pchambre/PC1500ExpansionModule/RP2350/monitor.c

/* monitor.c
 *
 * Ported from Design01_NonDMA_8K_PV_Swap.cydsn/main.c -- see that file
 * and this repo's plan history for the full background. Two halves,
 * now running on separate cores (changed 2026-09-17 -- see below):
 *
 *   1. monitor_run()'s bus loop (core0): on the GreenPAK's read-trigger
 *      (CS && Read && OE), drive the data pins from buffer[page][laddress];
 *      on the write-trigger (CS && Write), latch data into the buffer, or
 *      hand off to core1 if the write landed on the instruction address.
 *      Direct SIO register reads throughout (sio_hw->gpio_in/gpio_out/
 *      gpio_oe), not per-pin gpio_get()/gpio_put() calls -- those go
 *      through more machinery than a ~2us budget can afford. This loop
 *      never blocks, not even for a command's duration.
 *   2. monitor_command_worker()'s DoCommand() (core1): the same ~30-case
 *      EXP_COMMAND_* switch, translated case-by-case from SEGGER emFile's
 *      FS_* API to FatFs's f_* API. Blocks core1 for a command's whole
 *      duration; core0 is unaffected and keeps servicing the bus.
 *
 * RAM RESIDENCY -- deliberately NOT applied here. DoCommand() and this
 * file's loop don't need __not_in_flash_func the way qmi_cs1_spi.c/
 * qmi_cs1_sd.c do -- those needed it to keep their own internal per-byte
 * transfer loops from deadlocking against their own open QMI transaction
 * (see their own top comments), a QMI-specific hazard this design never
 * had to think about at all.
 *
 * WHY TWO CORES (changed 2026-09-17, was single-core): the original
 * single-core design had core0 call DoCommand() directly from inside the
 * bus loop, blocking the whole loop for the command's duration -- on the
 * theory (matching the PSoC5 original, which really does work this way)
 * that any bus read landing on the status byte *while DoCommand() runs*
 * would see whatever was last physically latched on the data pins, and
 * the ROM-side poll loop would just keep spinning until a real answer
 * came back once DoCommand() returned. That theory doesn't hold on this
 * board: this design releases the data bus to Hi-Z with a pull-DOWN
 * between transactions (see InitGpio()'s own comment), so "whatever was
 * last latched" during a long DoCommand() call is actually a floating
 * bus reading as 0x00 -- which is EXP_STATUS_READY's own value (see
 * pc_exp.h), completely indistinguishable from a real "done" answer.
 * Confirmed live 2026-09-17: SDLS's own SD_LIST_POLL busy-wait (rom.asm)
 * would see this false READY almost immediately, read directory data
 * DoCommand() hadn't written yet, and crash with a different garbage-
 * triggered BASIC error (ERROR 40/120/122, never the same one twice)
 * every time. A same-core fix (core0 explicitly driving EXP_STATUS_BUSY
 * and holding it for the whole call) was tried first and worked, but
 * still left core0 unable to service anything else for a command's whole
 * duration -- moving DoCommand() to core1 removes that limitation
 * entirely rather than just papering over its one known symptom.
 */
#include "monitor.h"

#include <stdio.h>
#include <string.h>

#include "hardware/structs/sio.h"
#include "hardware/gpio.h"
#include "hardware/sync.h"
#include "hardware/pio.h"
#include "hardware/dma.h"
#include "pico/stdlib.h"
#include "pico/time.h"
#ifndef PC1500_NO_CYW43
#include "pico/cyw43_arch.h"
/* The activity LED: a CYW43 GPIO on the dongle. */
#define LED_PUT(on) cyw43_arch_gpio_put(CYW43_WL_GPIO_LED_PIN, (on))
#else
#define LED_PUT(on) ((void)(on)) /* the internal card has no LED (2026-10-09) */
#endif
#include "pico/multicore.h"
#include "pico/low_power.h"
#include "pico/aon_timer.h"
#include "hardware/powman.h"
#include "hardware/watchdog.h"
#include "hardware/structs/scb.h"

#include "ff.h"
#include "board_pins.h"
#include "pc_exp.h"
#include "greenpak_i2c.h"
#include "greenpak_virtual_io.h"
#include "mcu_log.h"
#include "keywords.h"
#include "kbd_seq.h"
#include "kbd_host.h"
#include "ble_link.h"
#include "wifi_link.h"
#include "ssh_session.h"
#include "net_ping.h"
#include "time_sync.h"
#include "history_session.h"
#include "basic_xlate.h"
#include "mcu_config.h"
#include "mcu_store.h"
#include "read_serve.pio.h"
#include "write_serve.pio.h"

/* rom_image.h is generated by ../Design01_NonDMA_8K_PV_Swap.cydsn/rom/
 * build.ps1 from rom.asm -- the LH5801-side ROM content is identical
 * regardless of which MCU serves it, so this includes that same
 * generated file directly (CMakeLists.txt adds its directory to the
 * include path) rather than hand-copying it, so it can never drift from
 * the PSoC5 side. It uses PSoC's uint8/uint16 typedefs (normally pulled
 * in via project.h there); #define'd here just for this include so the
 * generated file itself doesn't need touching. */
#define uint8 uint8_t
#define uint16 uint16_t
#include "rom_image.h"
#undef uint8
#undef uint16

/* ---- Shared 8K data window: pages 0-7 (2K live data window) plus
 * pages 8-31 (6K ROM region, only actually driven through this buffer
 * while Control_Mode_Control-equivalent GreenPAK state selects
 * ROM_FROM_MCU during the boot copy -- see PC_EXP.h's own top comment).
 *
 * 8192-byte aligned (2026-09-18) -- the PIO-driven read path
 * (read_serve.pio's addr_capture program, see SetupReadServePio() below)
 * builds a complete absolute RAM address by shifting a fixed prefix (this
 * buffer's own high address bits) ahead of the live 13-bit address bus
 * value. That only produces the right address if this buffer's base
 * address has all ADDR_PIN_COUNT low bits clear -- i.e. is aligned to its
 * own size (8192 = 2^13). GCC/Clang's `aligned` attribute on a static
 * array guarantees the linker places it on that boundary. */
static uint8_t buffer[32][256] __attribute__((aligned(8192)));

/* Command watchdog, checked by core0 (never core1 -- core1 may be deep
 * inside a blocked call and can't watch its own clock). `buffer`'s status
 * byte is the single source of truth for "a command is in flight" (==
 * EXP_STATUS_BUSY); g_command_start_us is only meaningful while that's
 * true, refreshed every time core0 dispatches a new command. This is a
 * backstop, not the primary fix -- greenpak_i2c.c's own I2C_SCL_TIMEOUT_US
 * bound (2026-09-17) already converts the one known unbounded hang into a
 * fast, clean failure. This catches anything that's merely slow (or any
 * future bug in the same class) by forcing the status to ERROR once a
 * command has been running too long, so the LH5801's own busy-poll loop
 * (which has no timeout of its own) always gets an answer.
 *
 * Widened from the original 2s (2026-09-17) -- that value was chosen for
 * SDLS specifically and directly broke the DOSTUFF isolation test it was
 * never meant to cover: DOSTUFF 5/8 were firing this watchdog at 2s,
 * forcing ERROR while core1 kept legitimately sleeping in the background,
 * then racing core1's own late real WriteStatus() against this one for
 * whichever value the LH5801's next poll happened to sample -- exactly
 * the inconsistent BAD STATUS/OK results seen live. 30s comfortably
 * covers DOSTUFF's own test range; this still needs to become per-command
 * eventually (SDLS itself only needs ~2s worst case -- see
 * diskio_sd.c's SD_INIT_TIMEOUT_US -- so 30s is far looser than
 * ideal for real commands, just deliberately out of DOSTUFF's way for now).
 * NOTE: this does not free up core1 if it's genuinely wedged -- it only
 * lets the bus/LH5801 side recover. A wedged core1 still won't process
 * any later command until reset, unless/until the low-level blocking
 * calls are changed to cooperatively check an abort flag themselves. */
#define COMMAND_TIMEOUT_US 30000000u
static uint32_t g_command_start_us = 0;

/* See monitor.h's own comment. Definition lives here since monitor_run()
 * (this file) is the only reader/toggler; greenpak_i2c.c is the writer. */
volatile bool g_i2c_activity_pending = false;

/* See monitor.h's own comment. Definition lives here since monitor_run()
 * is the only reader; WriteStatus() (this file, below) is the writer. */
volatile bool g_command_done_pending = false;

/* Ported from Design01_NonDMA_8K_PV_Swap.cydsn/main.c's InitBuffer/
 * LoadRomImage: zeroes the shared window, then memcpys each sparse
 * chunk of kRomImageData into place at its kRomImageChunks offset.
 * Must run before monitor_run() starts servicing bus reads (main.c's
 * job, before launching core1) -- otherwise the ROM region reads back
 * as whatever main.c's caller catches. */
void monitor_init_buffer(void) {
    memset(buffer, 0, sizeof(buffer));
    const uint8_t *src = kRomImageData;
    uint8_t *base = &buffer[0][0];
    for (size_t i = 0; i < sizeof(kRomImageChunks) / sizeof(kRomImageChunks[0]); i++) {
        memcpy(base + kRomImageChunks[i].offset, src, kRomImageChunks[i].length);
        src += kRomImageChunks[i].length;
    }
    /* READY is no longer 0 (pc_exp.h, 2026-09-24), so the memset above no
     * longer leaves the status cell reading READY by accident. */
    buffer[EXP_INSTRUCTION_PAGE][EXP_INSTRUCTION_ADDRESS] = EXP_STATUS_READY;
}

static FIL currentFile;
static bool currentFileOpen = false;
static uint8_t currentFileStatus = EXP_SD_FILE_STATUS_CLOSED;
static uint32_t fileEnd = 0;
static char currentFileName[64];

/* After a POWMAN wake (MCONF POWMANDELAY, "STAGE RAM sleep" below): the
 * directory to go back to at the first SD command. core1. */
static char g_cwd_restore[20 + 1];

static FIL channelFile[EXP_MAX_SD_CHANNELS];
static bool channelOpen[EXP_MAX_SD_CHANNELS];
static char channelName[EXP_MAX_SD_CHANNELS][EXP_PATH_ARG_LEN + 1];
static uint32_t channelReadPos[EXP_MAX_SD_CHANNELS];

/* See monitor.h. The FIL objects themselves need no closing: FatFs
 * re-mounts the new card with a fresh volume id, so any operation on an
 * old handle already fails with FR_INVALID_OBJECT. */
void monitor_sd_card_changed(void) {
    currentFileOpen = false;
    currentFileStatus = EXP_SD_FILE_STATUS_CLOSED;
    fileEnd = 0;
    for (int i = 0; i < EXP_MAX_SD_CHANNELS; i++) {
        channelOpen[i] = false;
        channelReadPos[i] = 0;
    }
}

/* STAGE keyword state (2026-09) -- GreenPAK1/GreenPAK2 share one
 * physical I2C bus (board_pins.h's PIN_GREENPAK1_SDA/SCL alias), so one
 * bus struct serves both chips, distinguished by addr7 per call.
 * romCopyActive/romCopyBlockIndex track an in-progress
 * ROM_COPY_BEGIN..GET_BLOCK*..FINISH sequence so GET_BLOCK can refuse a
 * call that arrives without a matching BEGIN (or after 6 blocks already
 * landed), and so FINISH/a later FROM_MCU can reset it. */
static const greenpak_i2c_bus_t g_greenpak_bus = {
    .sda_gpio = PIN_GREENPAK1_SDA,
    .scl_gpio = PIN_GREENPAK1_SCL,
};
static bool romCopyActive = false;
static uint16_t romCopyBlockIndex = 0;

/* True only after a full STAGE copy finished with a matching whole-ROM
 * checksum (ROM_COPY_FINISH success) and nothing has since reverted or
 * restarted it (2026-09-24). Remap alone can't answer "is the SRAM copy
 * good?" -- a failed STAGE DEBUG deliberately leaves Remap engaged over a
 * partial copy -- so ROM_GET_MODE reports this alongside Remap, letting
 * the ROM's boot hook (and STAGE RAM) skip re-staging on every reset/power-
 * on. Cleared at RP2350 boot too, matching monitor_init_greenpak()'s own
 * forced Remap-off. */
static volatile bool romStagedVerified = false; /* written by core1, read by core0 (sleep decisions) */

/* Set by core1's EXP_COMMAND_DONE (only while romStagedVerified), consumed
 * by core0's monitor_run() loop -- see the "STAGE RAM sleep" section. */
static volatile bool g_sleep_requested = false;
/* When DONE set g_sleep_requested -- the MCONF SLEEPWAIT delay counts from
 * here. */
static volatile uint32_t g_sleep_requested_us;

/* Boot-time problem for MLOG, if any -- monitor_init_greenpak() runs
 * before mcu_log_init() and before core1 exists, so it can't write the
 * flash-backed log itself; monitor_command_worker() logs it on start. */
static const char *g_boot_remap_log = NULL;

/* See monitor.h's own comment. Keeps a staged ROM across a power cycle
 * (2026-09-25, board owner's call): the GreenPAKs and the SRAM stay powered
 * from VGG while the PC-1500 -- and now the Pico with it -- is off, so a
 * finished STAGE survives. Trusted when both Remap bits are set and GP1's
 * write-enable is clear (FINISH clears WE, so a set WE means the copy was
 * interrupted). Anything else reverts all three virtual inputs to MCU-
 * served ROM, as this function always used to unconditionally: a failed or
 * interrupted STAGE otherwise leaves Remap on over half-written SRAM, and
 * that survives an RP2350 reset. Remap bits that disagree, or a set WE, are
 * logged. Known gap: a STAGE DEBUG whose final checksum failed leaves Remap
 * on and WE clear over a bad copy, and is trusted here. */
void monitor_init_greenpak(void) {
    greenpak_i2c_init(&g_greenpak_bus);
    romCopyActive = false;

    bool remap1 = false, remap2 = false, we = false;
    bool ok = greenpak_virtual_input_get(&g_greenpak_bus, GREENPAK_GP1_I2C_ADDR, GP1_VI_SRAM_ROM_REMAP, &remap1)
           && greenpak_virtual_input_get(&g_greenpak_bus, GREENPAK_GP2_I2C_ADDR, GP2_VI_SRAM_ROM_REMAP, &remap2)
           && greenpak_virtual_input_get(&g_greenpak_bus, GREENPAK_GP1_I2C_ADDR, GP1_VI_SRAM_ROM_WE, &we);
    if (ok && remap1 && remap2 && !we) {
        romStagedVerified = true; /* keep the staged ROM -- the boot hook skips the copy */
        return;
    }

    if (!ok) g_boot_remap_log = "BOOT GP read failed";
    else if (remap1 != remap2) g_boot_remap_log = "BOOT GP1/GP2 remap diff";
    else if (we) g_boot_remap_log = "BOOT copy incomplete";
    greenpak_virtual_input_set(&g_greenpak_bus, GREENPAK_GP1_I2C_ADDR, GP1_VI_SRAM_ROM_REMAP, false);
    greenpak_virtual_input_set(&g_greenpak_bus, GREENPAK_GP2_I2C_ADDR, GP2_VI_SRAM_ROM_REMAP, false);
    greenpak_virtual_input_set(&g_greenpak_bus, GREENPAK_GP1_I2C_ADDR, GP1_VI_SRAM_ROM_WE, false);
    romStagedVerified = false;
}

/* Same 16-bit additive checksum as rom.asm's STAGE_COPY_ROUTINE_ABS
 * checksum loop -- natural unsigned wraparound on both sides, no
 * multiply needed on either (the LH5801 has none). */
static uint16_t ComputeRomChecksum(uint8_t buf[16][256]) {
    uint16_t sum = 0;
    for (uint8_t page = 8; page < 32; page++) {
        for (uint16_t i = 0; i < 256; i++) {
            sum = (uint16_t)(sum + buf[page][i]);
        }
    }
    return sum;
}

/* Same algorithm as ComputeRomChecksum, scoped to just the 1024-byte
 * payload window (pages 0-3) -- see EXP_BLOCK_CHECKSUM_PAGE's own comment
 * in pc_exp.h for why this exists: a per-block SRAM readback check,
 * independent of (and finer-grained than) ComputeRomChecksum's
 * whole-image one. */
static uint16_t ComputeBlockChecksum(uint8_t buf[16][256]) {
    uint16_t sum = 0;
    for (uint8_t page = 0; page < 4; page++) {
        for (uint16_t i = 0; i < 256; i++) {
            sum = (uint16_t)(sum + buf[page][i]);
        }
    }
    return sum;
}

/* ============================================================
 * Buffer/string helpers -- filesystem-API-agnostic, ported verbatim
 * from main.c. (DataFromBuffer is not ported: it's dead code in the
 * original too, referenced only from a commented-out call.)
 * ============================================================ */

/* A BASIC load's chunk just read (the length port says how much): its
 * CE-150 codes made this module's own, the count adjusted (basic_xlate.h). */
static void TranslateRead(uint8_t buf[16][256]) {
    uint16_t n;
    if (basic_xlate_mode() != BASIC_XLATE_LOAD) return;
    n = (uint16_t)((buf[EXP_LENGTH_PORT_PAGE][EXP_LENGTH_PORT_ADDRESS] << 8) +
                   buf[EXP_LENGTH_PORT_PAGE][EXP_LENGTH_PORT_ADDRESS + 1]);
    n = basic_xlate_read(&buf[EXP_BUFFER_START_PAGE][EXP_BUFFER_START_ADDRESS], n);
    buf[EXP_LENGTH_PORT_PAGE][EXP_LENGTH_PORT_ADDRESS] = (uint8_t)(n >> 8);
    buf[EXP_LENGTH_PORT_PAGE][EXP_LENGTH_PORT_ADDRESS + 1] = (uint8_t)n;
}

static void LongToBuffer(uint8_t buf[16][256], int8_t page, int8_t start, uint32_t value) {
    buf[page][start] = (uint8_t)((value >> 24) & 0xFF);
    buf[page][start + 1] = (uint8_t)((value >> 16) & 0xFF);
    buf[page][start + 2] = (uint8_t)((value >> 8) & 0xFF);
    buf[page][start + 3] = (uint8_t)(value & 0xFF);
}

static void StringFromBuffer(uint8_t buf[16][256], uint8_t page, uint8_t start, uint16_t length,
                              char result[]) {
    const uint8_t *b = &buf[page][start];
    for (uint16_t i = 0; i < length; i++) result[i] = (char)*b++;
    result[length] = 0;
}

static void FormatSizeText(uint32_t value, uint8_t result[], uint8_t width) {
    uint8_t i;
    for (i = 0; i < width; i++) result[i] = ' ';
    i = width;
    do {
        i--;
        result[i] = (uint8_t)('0' + (value % 10));
        value /= 10;
    } while (value != 0 && i > 0);
}

static uint8_t WriteDecimal(uint32_t value, uint8_t result[]) {
    uint8_t buf[10];
    uint8_t n = 0;
    uint8_t i;
    if (value == 0) {
        result[0] = '0';
        return 1;
    }
    while (value != 0) {
        buf[n++] = (uint8_t)('0' + (value % 10));
        value /= 10;
    }
    for (i = 0; i < n; i++) result[i] = buf[n - 1 - i];
    return n;
}

/* Fixed 4-digit uppercase hex -- for EXP_COMMAND_LOG_BLOCK_CHECKSUM's
 * mismatch report (see below): compact enough to fit both the expected
 * and found 16-bit checksums plus the block index in MCU_LOG_MSG_MAX. */
static uint8_t WriteHex4(uint16_t value, uint8_t result[]) {
    static const char hexDigits[] = "0123456789ABCDEF";
    result[0] = (uint8_t)hexDigits[(value >> 12) & 0xF];
    result[1] = (uint8_t)hexDigits[(value >> 8) & 0xF];
    result[2] = (uint8_t)hexDigits[(value >> 4) & 0xF];
    result[3] = (uint8_t)hexDigits[value & 0xF];
    return 4;
}

/* Same as WriteHex4, for a single byte -- STAGE DEBUG's per-byte mismatch
 * report needs both a 16-bit address and two separate 8-bit values. */
static uint8_t WriteHex2(uint8_t value, uint8_t result[]) {
    static const char hexDigits[] = "0123456789ABCDEF";
    result[0] = (uint8_t)hexDigits[(value >> 4) & 0xF];
    result[1] = (uint8_t)hexDigits[value & 0xF];
    return 2;
}

/* Human-readable byte count (B/K/M/G, 1024-based, 2 decimal digits above
 * B) -- SDDF used to show a raw byte count directly (e.g.
 * "2122343424F / 3221225472T"), confirmed hard to read at a glance on
 * real hardware, 2026-09-19. Integer-only (no float/double), same
 * convention as WriteDecimal/FormatSizeText elsewhere in this file --
 * this MCU has an FPU, but there's no reason to need one for a fixed
 * 2-decimal-digit format. `result` must have room for up to 10 bytes
 * (e.g. "1023.99G"). */
static uint8_t FormatHumanBytes(uint32_t bytes, uint8_t result[]) {
    static const char kUnits[4] = { 'B', 'K', 'M', 'G' };
    uint32_t divisor = 1;
    uint8_t unit = 0;
    while (bytes / divisor >= 1024 && unit < 3) {
        divisor *= 1024;
        unit++;
    }
    uint8_t pos = WriteDecimal(bytes / divisor, result);
    if (unit > 0) {
        uint32_t remainder = bytes % divisor;
        uint32_t frac = (uint32_t)(((uint64_t)remainder * 100u) / divisor);
        result[pos++] = '.';
        result[pos++] = (uint8_t)('0' + (frac / 10));
        result[pos++] = (uint8_t)('0' + (frac % 10));
    }
    result[pos++] = (uint8_t)kUnits[unit];
    return pos;
}

static void FormatSummaryLine(uint16_t count, uint32_t totalBytes, uint32_t freeBytes,
                               uint8_t result[], uint8_t width) {
    char temp[48];
    uint8_t pos = 0;
    uint8_t i;
    pos = (uint8_t)(pos + WriteDecimal(count, (uint8_t *)(temp + pos)));
    temp[pos++] = ' ';
    temp[pos++] = 'F';
    temp[pos++] = 'I';
    temp[pos++] = 'L';
    temp[pos++] = 'E';
    temp[pos++] = 'S';
    temp[pos++] = ' ';
    /* Human-readable (B/K/M/G, see FormatHumanBytes's own comment) --
     * same fix as SDDF's, and for the same reason: a raw byte count here
     * was confirmed hard to read at a glance, 2026-09-19/20. FormatHumanBytes
     * already ends with a real unit letter (B if under 1024, else K/M/G),
     * so no separate literal 'B' after totalBytes like the old format
     * had -- but freeBytes still gets a distinguishing " F" after it
     * (matching SDDF's own " F"/" T" convention), since without it
     * there'd be no way to tell the two numbers apart at a glance. */
    pos = (uint8_t)(pos + FormatHumanBytes(totalBytes, (uint8_t *)(temp + pos)));
    temp[pos++] = ' ';
    pos = (uint8_t)(pos + FormatHumanBytes(freeBytes, (uint8_t *)(temp + pos)));
    temp[pos++] = ' ';
    temp[pos++] = 'F';
    for (i = 0; i < width; i++) result[i] = (i < pos) ? (uint8_t)temp[i] : ' ';
}

/* Same as FormatSummaryLine() but omits the free-space figure entirely
 * (2026-09-21, per the board owner) -- SDLS on this board (the
 * SC18IS602B-bridged Pico2W dongle) was calling GetVolumeSpace() purely
 * to populate that one number, and GetVolumeSpace()'s own f_getfree()
 * is what triggers FatFs's slow first-call full FAT scan (multi-second
 * on this dongle's I2C-bridged SD link -- the same slow path implicated
 * in this session's still-open LH5801-lockup investigation). SDLS is a
 * routine "what files are here" listing, not a deliberate "how much
 * space is left" request, so it shouldn't have to pay that cost every
 * time; SDDF (EXP_COMMAND_GET_SD_DF_TEXT, untouched by this change)
 * remains available whenever the user actually wants free-space info,
 * a single explicit, deliberate command instead of an unavoidable tax
 * on every directory listing. `totalBytes` (the sum of this listing's
 * own file sizes, already computed for free while building the entries
 * -- no extra FAT scan needed) is kept, since it costs nothing extra.
 * Revisit once this board moves to the internal expansion card's real
 * SPI-attached SD (no I2C bridge in the way) -- GetVolumeSpace() should
 * be fast enough there to bring the free-space figure back
 * unconditionally. */
static void FormatSummaryLineNoFreeSpace(uint16_t count, uint32_t totalBytes, uint8_t result[],
                                          uint8_t width) {
    char temp[32];
    uint8_t pos = 0;
    uint8_t i;
    pos = (uint8_t)(pos + WriteDecimal(count, (uint8_t *)(temp + pos)));
    temp[pos++] = ' ';
    temp[pos++] = 'F';
    temp[pos++] = 'I';
    temp[pos++] = 'L';
    temp[pos++] = 'E';
    temp[pos++] = 'S';
    temp[pos++] = ' ';
    pos = (uint8_t)(pos + FormatHumanBytes(totalBytes, (uint8_t *)(temp + pos)));
    for (i = 0; i < width; i++) result[i] = (i < pos) ? (uint8_t)temp[i] : ' ';
}

/* MLOG VIEW support (2026-09-21) -- formats one mcu_log entry as a display
 * line ("E: <message>", space-padded/truncated to `width`), matching the
 * same "26 raw bytes, format-agnostic" convention SD_LIST_DISPLAY already
 * uses for both real directory entries and summary lines (see rom.asm's
 * own comment on that routine) -- LOG_LIST reuses SD_LIST_DISPLAY/UP/DOWN
 * verbatim rather than adding new ROM-side display code. */
static void FormatLogEntryLine(uint8_t level, const char *msg, uint8_t result[], uint8_t width) {
    char temp[MCU_LOG_MSG_MAX + 4];
    uint8_t pos = 0;
    temp[pos++] = (level == MCU_LOG_LEVEL_ERROR) ? 'E'
                : (level == MCU_LOG_LEVEL_WARN)  ? 'W'
                : (level == MCU_LOG_LEVEL_USER)  ? 'U'
                                                 : 'I';
    temp[pos++] = ':';
    temp[pos++] = ' ';
    uint8_t msgLen = (uint8_t)strlen(msg);
    for (uint8_t j = 0; j < msgLen; j++) temp[pos++] = msg[j];
    for (uint8_t i = 0; i < width; i++) result[i] = (i < pos) ? (uint8_t)temp[i] : ' ';
}

static void NormalizeSdPathFromFs(const char *raw, char *out, uint8_t outSize) {
    const char *colon = strchr(raw, ':');
    const char *src = colon ? colon + 1 : raw;
    uint8_t n = 0;
    out[n++] = '/';
    for (; *src != 0 && n < outSize - 1; src++) {
        char c = (*src == '\\') ? '/' : *src;
        if (n == 1 && c == '/') continue;
        out[n++] = c;
    }
    out[n] = 0;
}

static void ConvertSdPathToFsSeparators(char *path) {
    for (; *path != 0; path++)
        if (*path == '/') *path = '\\';
}

static void ConvertPlusToTilde(char *name) {
    for (; *name != 0; name++)
        if (*name == '+') *name = '~';
}

static void ConvertTildeToPlus(char *name) {
    for (; *name != 0; name++)
        if (*name == '~') *name = '+';
}

static void PrepareFsName(const char *raw, char *out, uint8_t outSize) {
    strncpy(out, raw, outSize - 1);
    out[outSize - 1] = 0;
    ConvertPlusToTilde(out);
    ConvertSdPathToFsSeparators(out);
}

static const char *GetBasename(const char *path) {
    const char *base = path;
    for (const char *p = path; *p != 0; p++)
        if (*p == '/' || *p == '\\') base = p + 1;
    return base;
}

/* FatFs equivalent of FS_GetFileAttributes(path) & FS_ATTR_DIRECTORY --
 * f_stat() failing (file doesn't exist) is treated as "not a directory",
 * same as the original's implicit behavior when the emFile call fails. */
static bool IsDirectory(const char *path) {
    FILINFO fno;
    if (f_stat(path, &fno) != FR_OK) return false;
    return (fno.fattrib & AM_DIR) != 0;
}

static void ResolveCopyOrMoveDestination(const char *srcBasename, const char *destArg, char *out,
                                          uint8_t outSize) {
    char converted[EXP_PATH_ARG_LEN + 1];
    PrepareFsName(destArg, converted, sizeof(converted));
    if (IsDirectory(converted)) {
        uint8_t n = 0;
        for (; converted[n] != 0 && n < outSize - 1; n++) out[n] = converted[n];
        if (n > 0 && out[n - 1] != '\\' && n < outSize - 1) out[n++] = '\\';
        uint8_t i = 0;
        while (srcBasename[i] != 0 && n < outSize - 1) out[n++] = srcBasename[i++];
        out[n] = 0;
    } else {
        strncpy(out, converted, outSize - 1);
        out[outSize - 1] = 0;
    }
}

/* FS_CopyFile has no FatFs equivalent -- manual read/write-loop copy. */
static bool CopyFileFatFs(const char *srcPath, const char *destPath) {
    FIL src, dst;
    if (f_open(&src, srcPath, FA_READ) != FR_OK) return false;
    if (f_open(&dst, destPath, FA_CREATE_ALWAYS | FA_WRITE) != FR_OK) {
        f_close(&src);
        return false;
    }
    uint8_t chunk[512];
    UINT br, bw;
    FRESULT fr = FR_OK;
    for (;;) {
        fr = f_read(&src, chunk, sizeof(chunk), &br);
        if (fr != FR_OK || br == 0) break;
        fr = f_write(&dst, chunk, br, &bw);
        if (fr != FR_OK || bw != br) {
            fr = FR_DISK_ERR;
            break;
        }
        if (br < sizeof(chunk)) break; /* short read == end of file */
    }
    f_close(&src);
    f_close(&dst);
    return fr == FR_OK;
}

/* FS_FSeek(file, offset, FS_SEEK_END) equivalent -- FatFs's f_lseek only
 * takes an absolute offset, so "seek to end" means seek to f_size(). */
static void SeekToEnd(FIL *fp) { f_lseek(fp, f_size(fp)); }

/* FS_GetVolumeFreeSpace/FS_GetVolumeSize equivalent, via the standard
 * FatFs idiom (f_getfree + fs->csize + sector size), not emFile's
 * single-call equivalents. */
static void GetVolumeSpace(uint32_t *totalBytes, uint32_t *freeBytes) {
    DWORD freeClusters = 0;
    FATFS *fs = NULL;
    if (f_getfree("", &freeClusters, &fs) != FR_OK || fs == NULL) {
        *totalBytes = 0;
        *freeBytes = 0;
        return;
    }
    printf("  [sd] GetVolumeSpace: fs_type=%u (2=FAT16 3=FAT32 4=exFAT) freeClusters=%lu\n",
           fs->fs_type, (unsigned long)freeClusters);
    *freeBytes = (uint32_t)freeClusters * fs->csize * FF_MAX_SS;
    *totalBytes = (uint32_t)(fs->n_fatent - 2) * fs->csize * FF_MAX_SS;
}

/* Keyword executor nesting (2026-09-25): while keywords.c runs ordinary
 * commands on its own behalf inside EXP_COMMAND_KEYWORD, their statuses
 * must not reach the status cell -- the LH5801 is still polling for the
 * keyword command's own result, and would take an inner SUCCESS for it.
 * WriteStatus() just records them for RunNestedCommand() instead. */
static int g_status_nesting;
static uint8_t g_nested_status;

static void WriteStatus(uint8_t buf[16][256], uint8_t status) {
    if (g_status_nesting > 0) {
        g_nested_status = status;
        return;
    }
    /* Barrier before publishing the status byte -- WriteStatus(SUCCESS)
     * (or ERROR/etc.) is always the LAST thing a DoCommand() case does,
     * after populating real data elsewhere in `buffer` (e.g.
     * EXP_COMMAND_LIST_SD_DIR writing the directory count/entries/summary
     * before its final WriteStatus() call). `buffer` is a plain,
     * non-volatile array shared between this core (core1) and core0's
     * bus loop, which serves LH5801 reads directly from it -- without
     * this, neither the compiler nor the hardware is obligated to make
     * those earlier writes visible to core0 before this one lands, so
     * the LH5801 could correctly see a non-BUSY status yet still read
     * stale/torn directory data underneath it. Plausible root cause
     * (2026-09-17, pre-dating and independent of the HLT polling
     * experiment) for ERROR 122/garbage-on-screen after SDLS -- a
     * genuine cross-core visibility gap, not the busy-wait mechanism
     * itself.
     *
     * __dmb() -> __dsb() (2026-09-21, board owner's own diagnosis after
     * STAGE DEBUG's per-byte SRAM verify kept reporting expected/found
     * values that matched NEITHER each other NOR the real ROM content --
     * "reading the ROM [the static region, populated once at boot, long
     * settled by the time anything reads it] seems pretty reliable... I
     * think it's a timing issue when serving data through the [freshly-
     * staged payload] window" instead): __dmb() only guarantees ORDERING
     * -- that this store becomes visible to another observer no earlier
     * than the writes before it, whenever those eventually land -- not
     * that the processor actually WAITS for those earlier writes to
     * finish landing before moving on. __dsb() is the stronger primitive:
     * it stalls execution until every explicit memory access before it
     * has genuinely completed, not just been ordered. For a large,
     * multi-hundred-byte publish (GET_BLOCK's own 1024-byte memcpy is
     * exactly this shape) immediately followed by "now it's safe to
     * read," ordering alone leaves a real window where the status flag
     * could become visible to a DMA-driven reader before every byte of
     * the payload it's vouching for has actually settled -- explaining
     * corruption that gets worse deeper into a large transfer (STAGE
     * DEBUG's own per-byte case) without needing any fault on the
     * read-serve PIO/DMA mechanism itself, which has no reason to behave
     * differently for freshly-written data versus the static ROM region
     * it already serves reliably. */
    __compiler_memory_barrier();
    __dsb();
    buf[EXP_INSTRUCTION_PAGE][EXP_INSTRUCTION_ADDRESS] = status;

    /* Drive-activity LED OFF signal -- see g_command_done_pending's own
     * comment in monitor.h. Every DoCommand() case's real, final status
     * write funnels through here, so this is the one place that can
     * reliably mean "busy just cleared" -- excludes DoCommand()'s own
     * redundant BUSY re-stamp at its top (monitor.h's own comment) and
     * core0's original BUSY stamp at dispatch time, neither of which
     * should turn the LED off.
     *
     * Also clears g_i2c_activity_pending here, from this same (core1)
     * side, rather than relying solely on core0's loop to have already
     * observed and cleared it first (2026-09-22, after real-hardware
     * reports of the LED staying on after a command that clearly
     * finished -- RAMTST2 on success, STAGE DEBUG on a real mismatch
     * failure). The original design's "done checked after activity, so
     * it wins if both land in the same iteration" only holds if core0's
     * loop actually gets to run an iteration between every activity-
     * pending set and this one -- not guaranteed, especially since core0
     * can be genuinely paused for a real stretch by flash_safe_execute()
     * during any mcu_log_error()/mcu_log_warn() call this same command
     * may have made (those are unconditional, unlike mcu_log_info(),
     * which needs MLOG VERBOSE -- STAGE's own byte-mismatch/FINISH-
     * failure paths call mcu_log_error() on every real failure). Clearing
     * both flags together, from the writer, makes "done" authoritative
     * regardless of core0's polling cadence: by the time core0 next
     * checks, there is no stale activity flag left for it to race
     * against. */
    if (status != EXP_STATUS_BUSY) {
        g_i2c_activity_pending = false;
        g_command_done_pending = true;
    }
}

/* ============================================================
 * DoCommand -- ~30-case switch, ported from main.c's DoCommand(),
 * FS_* -> f_*. Case-by-case commentary kept where the FatFs mapping
 * isn't 1:1; see this file's own header and RP2350/README.md for the
 * general notes (FS_RmDir/f_unlink-on-a-directory, FS_ChDir/FF_FS_RPATH,
 * FS_CopyFile/CopyFileFatFs, volume free/total via f_getfree).
 * ============================================================ */
static void DoCommand(uint8_t req, uint8_t buf[16][256]);

/* kw_command_fn for keywords.c -- see g_status_nesting. */
static uint8_t RunNestedCommand(uint8_t command, void *ctx) {
    g_status_nesting++;
    g_nested_status = EXP_STATUS_NOT_IMPLEMENTED;
    DoCommand(command, (uint8_t (*)[256])ctx);
    g_status_nesting--;
    return g_nested_status;
}

/* Puts back the window-resident ROM code (the STAGE copy routine and
 * ROM_RESET_REMAP at 0x8400) -- the longest listings run into it. Done at
 * the start of every keyword, so STAGE always finds it intact. */
static void RestoreWindowCode(void) {
    const uint8_t *src = kRomImageData;
    uint8_t *base = &buffer[0][0];
    for (size_t i = 0; i < sizeof(kRomImageChunks) / sizeof(kRomImageChunks[0]); i++) {
        if (kRomImageChunks[i].offset >= 0x400 && kRomImageChunks[i].offset < 0x800)
            memcpy(base + kRomImageChunks[i].offset, src, kRomImageChunks[i].length);
        src += kRomImageChunks[i].length;
    }
}

static void DoCommand(uint8_t req, uint8_t buf[16][256]) {
    WriteStatus(buf, EXP_STATUS_BUSY);
    kbd_host_trace_to_log(); /* a BLE keyboard's connection trace, if any (kbd_host.h) */
    if (g_cwd_restore[0] && req >= EXP_COMMAND_GET_SD_FREE_SPACE && req <= EXP_COMMAND_SD_CHANNEL_EOF) {
        f_chdir(g_cwd_restore); /* the directory kept across a POWMAN sleep */
        g_cwd_restore[0] = 0;
    }
    switch (req) {
        case EXP_COMMAND_ROM_FROM_SRAM: {
            /* Real GreenPAK I2C (2026-09, STAGE keyword) -- GP1/GP2's
             * NVM-programmed addresses are confirmed assigned on this
             * board (see greenpak_i2c.h), superseding the earlier
             * "not yet assigned" assumption this case used to carry.
             * Both chips need Remap set for the mux to fully switch
             * (GP2 has no WE-equivalent -- it only routes read/write
             * triggers to the MCU, per GreenPakTester/selftest.h's own
             * comment). Doesn't touch GP1 write-enable -- that's STAGE
             * RAM's own BEGIN/FINISH concern, not a bare mode switch's. */
            greenpak_i2c_init(&g_greenpak_bus);
            bool ok = greenpak_virtual_input_set(&g_greenpak_bus, GREENPAK_GP1_I2C_ADDR, GP1_VI_SRAM_ROM_REMAP, true)
                   && greenpak_virtual_input_set(&g_greenpak_bus, GREENPAK_GP2_I2C_ADDR, GP2_VI_SRAM_ROM_REMAP, true);
            if (ok) {
                bool v1 = false, v2 = false;
                ok = greenpak_virtual_input_get(&g_greenpak_bus, GREENPAK_GP1_I2C_ADDR, GP1_VI_SRAM_ROM_REMAP, &v1)
                  && greenpak_virtual_input_get(&g_greenpak_bus, GREENPAK_GP2_I2C_ADDR, GP2_VI_SRAM_ROM_REMAP, &v2)
                  && v1 && v2;
            }
            WriteStatus(buf, ok ? EXP_STATUS_SUCCESS : EXP_STATUS_ERROR);
            break;
        }
        case EXP_COMMAND_ROM_FROM_MCU: {
            /* Also clears GP1 write-enable as a safety measure (a
             * stray write could otherwise reach the SRAM's ROM copy
             * unnoticed while MCU-serving) and resets romCopyActive --
             * this case doubles as STAGE's own mid-copy/checksum-failure
             * recovery path (see rom.asm's STAGE_COPY_ROUTINE_ABS), not
             * just a normal mode switch. */
            greenpak_i2c_init(&g_greenpak_bus);
            bool ok = greenpak_virtual_input_set(&g_greenpak_bus, GREENPAK_GP1_I2C_ADDR, GP1_VI_SRAM_ROM_REMAP, false)
                   && greenpak_virtual_input_set(&g_greenpak_bus, GREENPAK_GP2_I2C_ADDR, GP2_VI_SRAM_ROM_REMAP, false)
                   && greenpak_virtual_input_set(&g_greenpak_bus, GREENPAK_GP1_I2C_ADDR, GP1_VI_SRAM_ROM_WE, false);
            romCopyActive = false;
            romStagedVerified = false;
            WriteStatus(buf, ok ? EXP_STATUS_SUCCESS : EXP_STATUS_ERROR);
            break;
        }
        case EXP_COMMAND_ROM_GET_MODE: {
            greenpak_i2c_init(&g_greenpak_bus);
            bool remap = false;
            bool ok = greenpak_virtual_input_get(&g_greenpak_bus, GREENPAK_GP1_I2C_ADDR, GP1_VI_SRAM_ROM_REMAP, &remap);
            if (ok) {
                buf[EXP_BUFFER_START_PAGE][EXP_BUFFER_START_ADDRESS] = remap ? 1 : 0;
                buf[EXP_BUFFER_START_PAGE][EXP_BUFFER_START_ADDRESS + 1] = (remap && romStagedVerified) ? 1 : 0;
                buf[EXP_BUFFER_START_PAGE][EXP_BUFFER_START_ADDRESS + 2] =
                    mcu_config_get(MCU_CONFIG_AUTOSTAGE) ? 1 : 0;
                /* the keyboard driver's arm flags (2026-10-07): bit 0 BLKBD (the
                 * external keyboard read), bit 1 the command history */
                buf[EXP_BUFFER_START_PAGE][EXP_BUFFER_START_ADDRESS + 3] =
                    (uint8_t)((mcu_config_get(MCU_CONFIG_BLKBD) ? 1 : 0) | (mcu_config_get(MCU_CONFIG_HISTORY) ? 2 : 0));
            }
            WriteStatus(buf, ok ? EXP_STATUS_SUCCESS : EXP_STATUS_ERROR);
            break;
        }
        case EXP_COMMAND_LOG_LIST: {
            /* Same wire shape as EXP_COMMAND_LIST_SD_DIR's own response --
             * see pc_exp.h's own comment. Newest entry first (index 0),
             * then a summary line so SD_LIST_DOWN has somewhere to land
             * past the real entries, matching every other listing in this
             * ROM. A listing holds at most EXP_DIR_MAX_ENTRIES, so with a
             * large log (MCONF LOGSIZE) this is the newest ones, and the
             * summary says how many there are in all. */
            uint8_t *window = &buf[EXP_BUFFER_START_PAGE][EXP_BUFFER_START_ADDRESS];
            uint32_t total = mcu_log_get_count();
            uint8_t count = total > EXP_DIR_MAX_ENTRIES ? EXP_DIR_MAX_ENTRIES : (uint8_t)total;
            window[0] = 0;
            window[1] = count;
            for (uint8_t i = 0; i < count; i++) {
                uint8_t level;
                char msg[MCU_LOG_MSG_MAX + 1];
                mcu_log_get_entry(i, &level, msg);
                uint8_t *entry = window + 2 + (uint16_t)i * EXP_DIR_RECORD_SIZE;
                FormatLogEntryLine(level, msg, entry, EXP_DIR_NAME_LEN + EXP_DIR_SIZE_TEXT_LEN);
                memset(entry + EXP_DIR_NAME_LEN + EXP_DIR_SIZE_TEXT_LEN, 0, 4);
            }
            uint16_t summaryOffset = (uint16_t)(2 + (uint16_t)count * EXP_DIR_RECORD_SIZE);
            uint8_t summary[EXP_DIR_SUMMARY_LEN];
            uint8_t pos = 0;
            memset(summary, ' ', sizeof summary);
            if (count < total) {
                /* "NEWEST 66 OF 12345" */
                memcpy(summary, "NEWEST ", 7);
                pos = 7;
                pos = (uint8_t)(pos + WriteDecimal(count, summary + pos));
                memcpy(summary + pos, " OF ", 4);
                pos = (uint8_t)(pos + 4);
                pos = (uint8_t)(pos + WriteDecimal(total, summary + pos));
            } else {
                pos = WriteDecimal(total, summary);
                memcpy(summary + pos, " ENTRIES", 8);
            }
            memcpy(window + summaryOffset, summary, sizeof summary);
            WriteStatus(buf, EXP_STATUS_SUCCESS);
            break;
        }
        case EXP_COMMAND_LOG_CLEAR: {
            mcu_log_clear();
            WriteStatus(buf, EXP_STATUS_SUCCESS);
            break;
        }
        case EXP_COMMAND_LOG_SET_INFO_ENABLED: {
            bool enabled = buf[EXP_BUFFER_START_PAGE][EXP_BUFFER_START_ADDRESS] != 0;
            mcu_log_set_info_enabled(enabled);
            WriteStatus(buf, EXP_STATUS_SUCCESS);
            break;
        }
        case EXP_COMMAND_LOG_USER_MESSAGE: {
            /* MLOGMSG -- see pc_exp.h. A string value chunk ('S', length,
             * characters) at +1, from either a literal or a string
             * variable; truncated to the log's own line width. */
            const uint8_t *chunk = &buf[EXP_BUFFER_START_PAGE][EXP_BUFFER_START_ADDRESS + 1];
            if (chunk[0] != 'S') {
                WriteStatus(buf, EXP_STATUS_ERROR);
                break;
            }
            uint8_t len = chunk[1];
            if (len > MCU_LOG_MSG_MAX) len = MCU_LOG_MSG_MAX;
            char msg[MCU_LOG_MSG_MAX + 1];
            memcpy(msg, &chunk[2], len);
            msg[len] = 0;
            mcu_log_user(msg);
            WriteStatus(buf, EXP_STATUS_SUCCESS);
            break;
        }
        case EXP_COMMAND_LOG_GET_INFO_ENABLED: {
            buf[EXP_BUFFER_START_PAGE][EXP_BUFFER_START_ADDRESS] = mcu_log_get_info_enabled() ? 1 : 0;
            WriteStatus(buf, EXP_STATUS_SUCCESS);
            break;
        }
        case EXP_COMMAND_ROM_COPY_BEGIN: {
            romStagedVerified = false; /* the SRAM copy is about to be overwritten */
            greenpak_i2c_init(&g_greenpak_bus);
            bool setOk = greenpak_virtual_input_set(&g_greenpak_bus, GREENPAK_GP1_I2C_ADDR, GP1_VI_SRAM_ROM_REMAP, true)
                      && greenpak_virtual_input_set(&g_greenpak_bus, GREENPAK_GP1_I2C_ADDR, GP1_VI_SRAM_ROM_WE, true)
                      && greenpak_virtual_input_set(&g_greenpak_bus, GREENPAK_GP2_I2C_ADDR, GP2_VI_SRAM_ROM_REMAP, true);
            bool v1 = false, v2 = false, v3 = false;
            bool ok = setOk;
            if (ok) {
                ok = greenpak_virtual_input_get(&g_greenpak_bus, GREENPAK_GP1_I2C_ADDR, GP1_VI_SRAM_ROM_REMAP, &v1)
                  && greenpak_virtual_input_get(&g_greenpak_bus, GREENPAK_GP1_I2C_ADDR, GP1_VI_SRAM_ROM_WE, &v2)
                  && greenpak_virtual_input_get(&g_greenpak_bus, GREENPAK_GP2_I2C_ADDR, GP2_VI_SRAM_ROM_REMAP, &v3)
                  && v1 && v2 && v3;
            }
            /* INFO-level trace through the whole STAGE sequence (2026-09-21,
             * per the board owner: "log setting virtual inputs, staging a
             * block... acknowledgement... that a block is done") -- off by
             * default (MLOG INFO OFF), meant to be turned on before
             * reproducing an intermittent failure, then read back via
             * MLOG VIEW. Only logged on the path that's ALREADY succeeded up
             * to that point -- a failed step already gets its own ERROR
             * entry below, so INFO here never duplicates/contradicts that. */
            if (setOk) mcu_log_info("STAGE set OK");
            if (ok) {
                mcu_log_info("STAGE verify OK");
                romCopyActive = true;
                romCopyBlockIndex = 0;
            } else {
                /* The board owner's own motivating example for LOG:
                 * a virtual-input set that didn't verify on readback
                 * (or the I2C write itself failing) is exactly the kind
                 * of internal failure a user has no other way to see
                 * evidence of. */
                mcu_log_error(setOk ? "STAGE BEGIN verify failed" : "STAGE BEGIN I2C set failed");
            }
            printf("STAGE BEGIN: setOk=%d ok=%d v1=%d v2=%d v3=%d\n", setOk, ok, v1, v2, v3);
            WriteStatus(buf, ok ? EXP_STATUS_SUCCESS : EXP_STATUS_ERROR);
            break;
        }
        case EXP_COMMAND_ROM_COPY_GET_BLOCK: {
            /* buffer[8..31] already holds the real ROM image via
             * monitor_init_buffer()/LoadRomImage() -- unlike RP2350B,
             * which has this as a separate open gap. Each block is 4
             * pages (4*256=1024 bytes), copied into the payload window
             * pages 0-3 (EXP_BUFFER_START_PAGE onward). */
            if (!romCopyActive || romCopyBlockIndex >= 6) {
                printf("STAGE GET_BLOCK: refused, romCopyActive=%d romCopyBlockIndex=%u\n",
                       romCopyActive, (unsigned)romCopyBlockIndex);
                mcu_log_error("STAGE GET_BLOCK refused");
                WriteStatus(buf, EXP_STATUS_ERROR);
                break;
            }
            /* Re-assert BUSY (with WriteStatus()'s own __dsb() barrier)
             * immediately before staging, mirroring EXP_COMMAND_READ_FROM_
             * SD_FILE's own established pattern -- that case does the same
             * right before its own data-populating step (f_read()), this
             * one didn't. DoCommand()'s own top-of-function WriteStatus(BUSY)
             * only vouches for writes BEFORE it, not the memcpy below, which
             * runs several instructions later -- so it provides no barrier
             * for this specific write at all. Testing a real-hardware
             * finding (2026-09-23, board owner's own diagnosis): after
             * STAGE DEBUG, EXP_BUFFER_START_ABS's first ~15 bytes on the
             * LH5801 side read back as stale pre-GET_BLOCK content (a
             * `POKE 2` into that address before running confirms it: the
             * poked 2 turns up at the SRAM destination too) even though a
             * standalone PEEK immediately after a GET_BLOCK-only CALL shows
             * correct data -- narrowing this to something MCU-side, specific
             * to how this command stages its data, not a generic PIO/DMA
             * read-timing issue (which would also affect SDLOAD's own
             * read-then-immediately-consume pattern, and doesn't). */
            printf("First byte of buf[0] before status busy: %02X\n", buf[0][0]);
            WriteStatus(buf, EXP_STATUS_BUSY);
            uint8_t srcPage = (uint8_t)(8 + romCopyBlockIndex * 4);
            for (uint8_t i = 0; i < 4; i++) {
                memcpy(buf[i], buf[srcPage + i], 256);
            }

            /* Per-block SRAM readback verification (2026-09-21) -- see
             * EXP_BLOCK_CHECKSUM_PAGE's own comment in pc_exp.h. Computed
             * over the payload window right after staging it, so this is
             * a checksum of exactly what the ROM is about to tin-copy,
             * before anything else has a chance to touch buf[0..3]. */
            uint16_t blockChecksum = ComputeBlockChecksum(buf);
            buf[EXP_BLOCK_CHECKSUM_PAGE][EXP_BLOCK_CHECKSUM_ADDRESS] = (uint8_t)(blockChecksum >> 8);
            buf[EXP_BLOCK_CHECKSUM_PAGE][EXP_BLOCK_CHECKSUM_ADDRESS + 1] = (uint8_t)(blockChecksum & 0xFF);
            printf("STAGE GET_BLOCK: served block %u (srcPage=%u, checksum=%u)\n",
                   (unsigned)romCopyBlockIndex, (unsigned)srcPage, (unsigned)blockChecksum);
            {
                /* "staging a block to be read by the LH5801" -- also
                 * doubles as an implicit "block N-1 acknowledged done" (the
                 * board owner's own third ask) whenever N>0: this call only
                 * happens because the LH5801's own copy loop finished its
                 * previous block and came back asking for the next one --
                 * there's no separate wire step where it explicitly says
                 * so, this MCU-side request IS that acknowledgement. If a
                 * real failure is "MLOG VIEW showed nothing, but COPY
                 * FAILED anyway" (like this session's own first real test),
                 * this trace directly shows the highest block number the
                 * MCU ever got asked for, which is exactly where to look on
                 * the LH5801/bus-timing side instead of the MCU side. */
                char msg[MCU_LOG_MSG_MAX + 1];
                uint8_t pos = 0;
                static const char prefix[] = "STAGE blk ";
                memcpy(msg, prefix, sizeof(prefix) - 1);
                pos = (uint8_t)(sizeof(prefix) - 1);
                pos = (uint8_t)(pos + WriteDecimal(romCopyBlockIndex, (uint8_t *)(msg + pos)));
                memcpy(msg + pos, " staged", 7);
                pos = (uint8_t)(pos + 7);
                msg[pos] = 0;
                mcu_log_info(msg);
            }
            romCopyBlockIndex++;
            buf[EXP_LENGTH_PORT_PAGE][EXP_LENGTH_PORT_ADDRESS] = (uint8_t)(EXP_MAX_TRANSFER_LEN >> 8);
            buf[EXP_LENGTH_PORT_PAGE][EXP_LENGTH_PORT_ADDRESS + 1] = (uint8_t)(EXP_MAX_TRANSFER_LEN & 0xFF);
            WriteStatus(buf, EXP_STATUS_SUCCESS);
            break;
        }
        case EXP_COMMAND_ROM_COPY_FINISH: {
            uint16_t reported = (uint16_t)((buf[EXP_BUFFER_START_PAGE][EXP_BUFFER_START_ADDRESS] << 8)
                                          | buf[EXP_BUFFER_START_PAGE][EXP_BUFFER_START_ADDRESS + 1]);
            uint16_t computed = ComputeRomChecksum(buf);
            bool checksumOk = (reported == computed);

            greenpak_i2c_init(&g_greenpak_bus);
            bool weOk = greenpak_virtual_input_set(&g_greenpak_bus, GREENPAK_GP1_I2C_ADDR, GP1_VI_SRAM_ROM_WE, false);
            if (weOk) {
                bool v = true;
                weOk = greenpak_virtual_input_get(&g_greenpak_bus, GREENPAK_GP1_I2C_ADDR, GP1_VI_SRAM_ROM_WE, &v) && !v;
            }
            romCopyActive = false;
            romStagedVerified = checksumOk && weOk;
            if (!checksumOk) mcu_log_error("STAGE FINISH bad checksum");
            else if (!weOk) mcu_log_error("STAGE FINISH WE clear failed");
            else mcu_log_info("STAGE FINISH OK");
            printf("STAGE FINISH: reported=%u computed=%u checksumOk=%d weOk=%d\n", reported, computed,
                   checksumOk, weOk);
            WriteStatus(buf, (checksumOk && weOk) ? EXP_STATUS_SUCCESS : EXP_STATUS_ERROR);
            break;
        }
        case EXP_COMMAND_LOG_BLOCK_CHECKSUM: {
            printf("First byte of buf[0] at start of block checksum stage: %02X\n", buf[0][0]);
            /* See EXP_BLOCK_CHECKSUM_PAGE's own comment in pc_exp.h.
             * Reported once per block, right after the ROM's copy
             * routine reads that block back from SRAM and compares it
             * against the checksum GET_BLOCK already staged above. On a
             * mismatch, the ROM also sends its own (found) checksum at
             * EXP_BUFFER_START_ABS+2/+3 -- the expected one is still
             * sitting at EXP_BLOCK_CHECKSUM_ABS from this same block's
             * own GET_BLOCK call (nothing else touches that page in
             * between), so both are available here without a wider
             * round trip. */
            uint8_t blockIndex = buf[EXP_BUFFER_START_PAGE][EXP_BUFFER_START_ADDRESS];
            bool matched = buf[EXP_BUFFER_START_PAGE][EXP_BUFFER_START_ADDRESS + 1] != 0;
            char msg[MCU_LOG_MSG_MAX + 1];
            uint8_t pos = 0;
            static const char prefix[] = "STAGE blk ";
            memcpy(msg, prefix, sizeof(prefix) - 1);
            pos = (uint8_t)(sizeof(prefix) - 1);
            pos = (uint8_t)(pos + WriteDecimal(blockIndex, (uint8_t *)(msg + pos)));
            if (matched) {
                memcpy(msg + pos, " cksum OK", 9);
                pos = (uint8_t)(pos + 9);
                msg[pos] = 0;
                mcu_log_info(msg);
            } else {
                /* "STAGE blk N EXXXX FYYYY" -- E=expected (what the MCU
                 * staged), F=found (what the ROM read back from SRAM).
                 * Exactly MCU_LOG_MSG_MAX (23) characters for a 1-digit
                 * block index (0-5), no truncation. */
                uint16_t expected = (uint16_t)((buf[EXP_BLOCK_CHECKSUM_PAGE][EXP_BLOCK_CHECKSUM_ADDRESS] << 8)
                                              | buf[EXP_BLOCK_CHECKSUM_PAGE][EXP_BLOCK_CHECKSUM_ADDRESS + 1]);
                uint16_t found = (uint16_t)((buf[EXP_BUFFER_START_PAGE][EXP_BUFFER_START_ADDRESS + 2] << 8)
                                           | buf[EXP_BUFFER_START_PAGE][EXP_BUFFER_START_ADDRESS + 3]);
                msg[pos++] = ' ';
                msg[pos++] = 'E';
                pos = (uint8_t)(pos + WriteHex4(expected, (uint8_t *)(msg + pos)));
                msg[pos++] = ' ';
                msg[pos++] = 'F';
                pos = (uint8_t)(pos + WriteHex4(found, (uint8_t *)(msg + pos)));
                msg[pos] = 0;
                mcu_log_error(msg);
            }
            printf("STAGE LOG_BLOCK_CHECKSUM: block=%u matched=%d\n", (unsigned)blockIndex, matched);
            WriteStatus(buf, EXP_STATUS_SUCCESS);
            break;
        }
        case EXP_COMMAND_STAGE_BYTE_MISMATCH: {
            /* See pc_exp.h's own comment. Request: 2-byte BE SRAM address,
             * 1-byte expected, 1-byte found, all at EXP_BUFFER_START_ABS.
             * No response payload (2026-09-21) -- this used to also write a
             * ready-to-display message back into the same buffer for the
             * ROM to blit immediately, but real-hardware testing found
             * that reading a same-transaction MCU response back this way
             * wasn't reliable (garbled on-screen text observed even when
             * the mcu_log_error() call below -- built from the exact same
             * data -- was later confirmed correct via MLOG VIEW). The ROM
             * now shows a static, ROM-resident message instead and relies
             * entirely on this log entry (a separate, already-proven-
             * reliable round trip) for the real detail. */
            uint16_t addr = (uint16_t)((buf[EXP_BUFFER_START_PAGE][EXP_BUFFER_START_ADDRESS] << 8) |
                                        buf[EXP_BUFFER_START_PAGE][EXP_BUFFER_START_ADDRESS + 1]);
            uint8_t expected = buf[EXP_BUFFER_START_PAGE][EXP_BUFFER_START_ADDRESS + 2];
            uint8_t found = buf[EXP_BUFFER_START_PAGE][EXP_BUFFER_START_ADDRESS + 3];
            char msg[26];
            uint8_t pos = 0;
            static const char prefix[] = "STAGE @";
            memcpy(msg, prefix, sizeof(prefix) - 1);
            pos = (uint8_t)(sizeof(prefix) - 1);
            pos = (uint8_t)(pos + WriteHex4(addr, (uint8_t *)(msg + pos)));
            memcpy(msg + pos, " E:", 3);
            pos = (uint8_t)(pos + 3);
            pos = (uint8_t)(pos + WriteHex2(expected, (uint8_t *)(msg + pos)));
            memcpy(msg + pos, " F:", 3);
            pos = (uint8_t)(pos + 3);
            pos = (uint8_t)(pos + WriteHex2(found, (uint8_t *)(msg + pos)));
            msg[pos] = 0;
            mcu_log_error(msg);
            printf("STAGE_BYTE_MISMATCH: addr=%04X expected=%02X found=%02X\n", addr, expected, found);
            WriteStatus(buf, EXP_STATUS_SUCCESS);
            break;
        }
        case EXP_COMMAND_GET_SD_FREE_SPACE: {
            WriteStatus(buf, EXP_STATUS_BUSY);
            uint32_t total, free_;
            GetVolumeSpace(&total, &free_);
            LongToBuffer(buf, EXP_BUFFER_START_PAGE, EXP_BUFFER_START_ADDRESS, free_);
            WriteStatus(buf, EXP_STATUS_SUCCESS);
            break;
        }
        case EXP_COMMAND_GET_SD_VOLUME_SIZE: {
            WriteStatus(buf, EXP_STATUS_BUSY);
            uint32_t total, free_;
            GetVolumeSpace(&total, &free_);
            LongToBuffer(buf, EXP_BUFFER_START_PAGE, EXP_BUFFER_START_ADDRESS, total);
            WriteStatus(buf, EXP_STATUS_SUCCESS);
            break;
        }
        case EXP_COMMAND_GET_SD_FILE_SIZE: {
            if (!currentFileOpen) {
                WriteStatus(buf, EXP_STATUS_ERROR);
                break;
            }
            WriteStatus(buf, EXP_STATUS_BUSY);
            uint32_t fileSize = (uint32_t)f_size(&currentFile);
            LongToBuffer(buf, EXP_BUFFER_START_PAGE, EXP_BUFFER_START_ADDRESS, fileSize);
            WriteStatus(buf, EXP_STATUS_SUCCESS);
            break;
        }
        case EXP_COMMAND_READ_SD_VOLUME_LABEL: {
            WriteStatus(buf, EXP_STATUS_BUSY);
            uint16_t volumeNameLen = buf[EXP_BUFFER_START_PAGE][EXP_BUFFER_START_ADDRESS] * 256 +
                                      buf[EXP_BUFFER_START_PAGE][EXP_BUFFER_START_ADDRESS + 1];
            if (volumeNameLen == 0) {
                WriteStatus(buf, EXP_STATUS_ERROR);
                break;
            }
            char volumeName[EXP_PATH_ARG_LEN + 1];
            if (volumeNameLen > EXP_PATH_ARG_LEN) volumeNameLen = EXP_PATH_ARG_LEN;
            StringFromBuffer(buf, EXP_BUFFER_START_PAGE, EXP_BUFFER_START_ADDRESS + 2,
                              volumeNameLen, volumeName);
            char label[34];
            if (f_getlabel(volumeName, label, NULL) != FR_OK) {
                WriteStatus(buf, EXP_STATUS_ERROR);
                break;
            }
            uint8_t labelLen = (uint8_t)strlen(label);
            buf[EXP_SCRATCH_PAGE][0] = labelLen;
            for (uint8_t i = 0; i < labelLen; i++) buf[EXP_SCRATCH_PAGE][i + 1] = label[i];
            WriteStatus(buf, EXP_STATUS_SUCCESS);
            break;
        }
        case EXP_COMMAND_GET_SD_FILE_NAME: {
            if (!currentFileOpen) {
                WriteStatus(buf, EXP_STATUS_ERROR);
                break;
            }
            WriteStatus(buf, EXP_STATUS_BUSY);
            uint8_t nameLen = (uint8_t)strlen(currentFileName);
            buf[EXP_SCRATCH_PAGE][0] = nameLen;
            for (uint8_t i = 0; i < nameLen; i++) buf[EXP_SCRATCH_PAGE][i + 1] = currentFileName[i];
            WriteStatus(buf, EXP_STATUS_SUCCESS);
            break;
        }
        case EXP_COMMAND_REMOVE_SD_FILE: {
            WriteStatus(buf, EXP_STATUS_BUSY);
            uint16_t rmNameLen = buf[EXP_BUFFER_START_PAGE][EXP_BUFFER_START_ADDRESS] * 256 +
                                  buf[EXP_BUFFER_START_PAGE][EXP_BUFFER_START_ADDRESS + 1];
            if (rmNameLen == 0) {
                WriteStatus(buf, EXP_STATUS_ERROR);
                break;
            }
            char rmName[EXP_PATH_ARG_LEN + 1];
            if (rmNameLen > EXP_PATH_ARG_LEN) rmNameLen = EXP_PATH_ARG_LEN;
            StringFromBuffer(buf, EXP_BUFFER_START_PAGE, EXP_BUFFER_START_ADDRESS + 2, rmNameLen,
                              rmName);
            char rmFsName[EXP_PATH_ARG_LEN + 1];
            PrepareFsName(rmName, rmFsName, sizeof(rmFsName));
            /* SDRM must only ever delete a file, never a directory --
             * SDRMDIR is the only sanctioned way to remove one. */
            if (IsDirectory(rmFsName)) {
                WriteStatus(buf, EXP_STATUS_ERROR);
                break;
            }
            WriteStatus(buf, f_unlink(rmFsName) == FR_OK ? EXP_STATUS_SUCCESS : EXP_STATUS_ERROR);
            break;
        }
        case EXP_COMMAND_CHANGE_SD_DIR: {
            WriteStatus(buf, EXP_STATUS_BUSY);
            uint16_t cdNameLen = buf[EXP_BUFFER_START_PAGE][EXP_BUFFER_START_ADDRESS] * 256 +
                                  buf[EXP_BUFFER_START_PAGE][EXP_BUFFER_START_ADDRESS + 1];
            if (cdNameLen == 0) {
                WriteStatus(buf, EXP_STATUS_ERROR);
                break;
            }
            char cdName[EXP_PATH_ARG_LEN + 1];
            if (cdNameLen > EXP_PATH_ARG_LEN) cdNameLen = EXP_PATH_ARG_LEN;
            StringFromBuffer(buf, EXP_BUFFER_START_PAGE, EXP_BUFFER_START_ADDRESS + 2, cdNameLen,
                              cdName);
            char cdFsName[EXP_PATH_ARG_LEN + 1];
            PrepareFsName(cdName, cdFsName, sizeof(cdFsName));
            WriteStatus(buf, f_chdir(cdFsName) == FR_OK ? EXP_STATUS_SUCCESS : EXP_STATUS_ERROR);
            break;
        }
        case EXP_COMMAND_MAKE_SD_DIR: {
            WriteStatus(buf, EXP_STATUS_BUSY);
            uint16_t mkNameLen = buf[EXP_BUFFER_START_PAGE][EXP_BUFFER_START_ADDRESS] * 256 +
                                  buf[EXP_BUFFER_START_PAGE][EXP_BUFFER_START_ADDRESS + 1];
            if (mkNameLen == 0) {
                WriteStatus(buf, EXP_STATUS_ERROR);
                break;
            }
            char mkName[EXP_PATH_ARG_LEN + 1];
            if (mkNameLen > EXP_PATH_ARG_LEN) mkNameLen = EXP_PATH_ARG_LEN;
            StringFromBuffer(buf, EXP_BUFFER_START_PAGE, EXP_BUFFER_START_ADDRESS + 2, mkNameLen,
                              mkName);
            char mkFsName[EXP_PATH_ARG_LEN + 1];
            PrepareFsName(mkName, mkFsName, sizeof(mkFsName));
            WriteStatus(buf, f_mkdir(mkFsName) == FR_OK ? EXP_STATUS_SUCCESS : EXP_STATUS_ERROR);
            break;
        }
        case EXP_COMMAND_REMOVE_SD_DIR: {
            WriteStatus(buf, EXP_STATUS_BUSY);
            uint16_t rmdirNameLen = buf[EXP_BUFFER_START_PAGE][EXP_BUFFER_START_ADDRESS] * 256 +
                                     buf[EXP_BUFFER_START_PAGE][EXP_BUFFER_START_ADDRESS + 1];
            if (rmdirNameLen == 0) {
                WriteStatus(buf, EXP_STATUS_ERROR);
                break;
            }
            char rmdirName[EXP_PATH_ARG_LEN + 1];
            if (rmdirNameLen > EXP_PATH_ARG_LEN) rmdirNameLen = EXP_PATH_ARG_LEN;
            StringFromBuffer(buf, EXP_BUFFER_START_PAGE, EXP_BUFFER_START_ADDRESS + 2,
                              rmdirNameLen, rmdirName);
            char rmdirFsName[EXP_PATH_ARG_LEN + 1];
            PrepareFsName(rmdirName, rmdirFsName, sizeof(rmdirFsName));
            /* f_unlink() on a directory only succeeds if it's empty
             * (FR_DENIED otherwise) -- same semantics as emFile's
             * FS_RmDir, no extra check needed. f_rmdir is #define'd to
             * f_unlink in ff.h. */
            WriteStatus(buf, f_unlink(rmdirFsName) == FR_OK ? EXP_STATUS_SUCCESS : EXP_STATUS_ERROR);
            break;
        }
        case EXP_COMMAND_GET_SD_CWD: {
            WriteStatus(buf, EXP_STATUS_BUSY);
            char cwdRaw[64];
            char cwd[64];
            if (f_getcwd(cwdRaw, sizeof(cwdRaw)) != FR_OK) {
                WriteStatus(buf, EXP_STATUS_ERROR);
                break;
            }
            NormalizeSdPathFromFs(cwdRaw, cwd, sizeof(cwd));
            ConvertTildeToPlus(cwd);
            uint8_t cwdLen = (uint8_t)strlen(cwd);
            buf[EXP_SCRATCH_PAGE][0] = cwdLen;
            for (uint8_t i = 0; i < cwdLen; i++) buf[EXP_SCRATCH_PAGE][i + 1] = cwd[i];
            WriteStatus(buf, EXP_STATUS_SUCCESS);
            break;
        }
        case EXP_COMMAND_COPY_SD_FILE: {
            WriteStatus(buf, EXP_STATUS_BUSY);
            uint8_t *window = &buf[EXP_BUFFER_START_PAGE][EXP_BUFFER_START_ADDRESS];
            uint16_t srcLen = (uint16_t)window[0] * 256 + window[1];
            uint16_t destLen = (uint16_t)window[EXP_TWO_NAME_SLOT_LEN] * 256 +
                                window[EXP_TWO_NAME_SLOT_LEN + 1];
            if (srcLen == 0 || destLen == 0 || srcLen > EXP_PATH_ARG_LEN ||
                destLen > EXP_PATH_ARG_LEN) {
                WriteStatus(buf, EXP_STATUS_ERROR);
                break;
            }
            char srcArg[EXP_PATH_ARG_LEN + 1], destArg[EXP_PATH_ARG_LEN + 1];
            for (uint16_t i = 0; i < srcLen; i++) srcArg[i] = (char)window[2 + i];
            srcArg[srcLen] = 0;
            for (uint16_t i = 0; i < destLen; i++)
                destArg[i] = (char)window[EXP_TWO_NAME_SLOT_LEN + 2 + i];
            destArg[destLen] = 0;
            char srcFsName[EXP_PATH_ARG_LEN + 1];
            PrepareFsName(srcArg, srcFsName, sizeof(srcFsName));
            char destFsName[EXP_PATH_ARG_LEN + 16];
            ResolveCopyOrMoveDestination(GetBasename(srcArg), destArg, destFsName,
                                          sizeof(destFsName));
            WriteStatus(buf, CopyFileFatFs(srcFsName, destFsName) ? EXP_STATUS_SUCCESS
                                                                    : EXP_STATUS_ERROR);
            break;
        }
        case EXP_COMMAND_MOVE_SD_FILE: {
            WriteStatus(buf, EXP_STATUS_BUSY);
            uint8_t *window = &buf[EXP_BUFFER_START_PAGE][EXP_BUFFER_START_ADDRESS];
            uint16_t srcLen = (uint16_t)window[0] * 256 + window[1];
            uint16_t destLen = (uint16_t)window[EXP_TWO_NAME_SLOT_LEN] * 256 +
                                window[EXP_TWO_NAME_SLOT_LEN + 1];
            if (srcLen == 0 || destLen == 0 || srcLen > EXP_PATH_ARG_LEN ||
                destLen > EXP_PATH_ARG_LEN) {
                WriteStatus(buf, EXP_STATUS_ERROR);
                break;
            }
            char srcArg[EXP_PATH_ARG_LEN + 1], destArg[EXP_PATH_ARG_LEN + 1];
            for (uint16_t i = 0; i < srcLen; i++) srcArg[i] = (char)window[2 + i];
            srcArg[srcLen] = 0;
            for (uint16_t i = 0; i < destLen; i++)
                destArg[i] = (char)window[EXP_TWO_NAME_SLOT_LEN + 2 + i];
            destArg[destLen] = 0;
            char srcFsName[EXP_PATH_ARG_LEN + 1];
            PrepareFsName(srcArg, srcFsName, sizeof(srcFsName));
            char destFsName[EXP_PATH_ARG_LEN + 16];
            ResolveCopyOrMoveDestination(GetBasename(srcArg), destArg, destFsName,
                                          sizeof(destFsName));
            WriteStatus(buf, f_rename(srcFsName, destFsName) == FR_OK ? EXP_STATUS_SUCCESS
                                                                        : EXP_STATUS_ERROR);
            break;
        }
        case EXP_COMMAND_CHECK_SD_COPY_MOVE_DEST_EXISTS: {
            WriteStatus(buf, EXP_STATUS_BUSY);
            uint8_t *window = &buf[EXP_BUFFER_START_PAGE][EXP_BUFFER_START_ADDRESS];
            uint16_t srcLen = (uint16_t)window[0] * 256 + window[1];
            uint16_t destLen = (uint16_t)window[EXP_TWO_NAME_SLOT_LEN] * 256 +
                                window[EXP_TWO_NAME_SLOT_LEN + 1];
            if (srcLen == 0 || destLen == 0 || srcLen > EXP_PATH_ARG_LEN ||
                destLen > EXP_PATH_ARG_LEN) {
                WriteStatus(buf, EXP_STATUS_ERROR);
                break;
            }
            char srcArg[EXP_PATH_ARG_LEN + 1], destArg[EXP_PATH_ARG_LEN + 1];
            for (uint16_t i = 0; i < srcLen; i++) srcArg[i] = (char)window[2 + i];
            srcArg[srcLen] = 0;
            for (uint16_t i = 0; i < destLen; i++)
                destArg[i] = (char)window[EXP_TWO_NAME_SLOT_LEN + 2 + i];
            destArg[destLen] = 0;
            char destFsName[EXP_PATH_ARG_LEN + 16];
            ResolveCopyOrMoveDestination(GetBasename(srcArg), destArg, destFsName,
                                          sizeof(destFsName));
            FILINFO fno;
            WriteStatus(buf, f_stat(destFsName, &fno) == FR_OK ? EXP_STATUS_SUCCESS
                                                                 : EXP_STATUS_ERROR);
            break;
        }
        case EXP_COMMAND_SD_OPEN_CHANNEL: {
            WriteStatus(buf, EXP_STATUS_BUSY);
            uint8_t *window = &buf[EXP_BUFFER_START_PAGE][EXP_BUFFER_START_ADDRESS];
            uint8_t channel = window[0];
            if (channel < 1 || channel > EXP_MAX_SD_CHANNELS) {
                WriteStatus(buf, EXP_STATUS_ERROR);
                break;
            }
            uint16_t nameLen = (uint16_t)window[1] * 256 + window[2];
            if (nameLen == 0 || nameLen > EXP_PATH_ARG_LEN) {
                WriteStatus(buf, EXP_STATUS_ERROR);
                break;
            }
            char name[EXP_PATH_ARG_LEN + 1];
            for (uint16_t i = 0; i < nameLen; i++) name[i] = (char)window[3 + i];
            name[nameLen] = 0;
            char fsName[EXP_PATH_ARG_LEN + 1];
            PrepareFsName(name, fsName, sizeof(fsName));

            uint8_t idx = channel - 1;
            if (channelOpen[idx]) {
                f_close(&channelFile[idx]);
                channelOpen[idx] = false;
            }
            /* Open for combined read+append -- create if it doesn't
             * exist, never truncate one that does (FA_OPEN_ALWAYS). */
            channelOpen[idx] = f_open(&channelFile[idx], fsName, FA_READ | FA_WRITE | FA_OPEN_ALWAYS) == FR_OK;
            if (!channelOpen[idx]) {
                WriteStatus(buf, EXP_STATUS_ERROR);
                break;
            }
            strncpy(channelName[idx], name, EXP_PATH_ARG_LEN);
            channelName[idx][EXP_PATH_ARG_LEN] = 0;
            channelReadPos[idx] = 0;
            WriteStatus(buf, EXP_STATUS_SUCCESS);
            break;
        }
        case EXP_COMMAND_SD_CLOSE_CHANNEL: {
            WriteStatus(buf, EXP_STATUS_BUSY);
            uint8_t *window = &buf[EXP_BUFFER_START_PAGE][EXP_BUFFER_START_ADDRESS];
            uint8_t channel = window[0];
            if (channel == 0) {
                for (uint8_t i = 0; i < EXP_MAX_SD_CHANNELS; i++) {
                    if (channelOpen[i]) {
                        f_close(&channelFile[i]);
                        channelOpen[i] = false;
                    }
                    channelName[i][0] = 0;
                    channelReadPos[i] = 0;
                }
                WriteStatus(buf, EXP_STATUS_SUCCESS);
                break;
            }
            if (channel > EXP_MAX_SD_CHANNELS) {
                WriteStatus(buf, EXP_STATUS_ERROR);
                break;
            }
            uint8_t idx = channel - 1;
            if (channelOpen[idx]) {
                f_close(&channelFile[idx]);
                channelOpen[idx] = false;
            }
            channelName[idx][0] = 0;
            channelReadPos[idx] = 0;
            WriteStatus(buf, EXP_STATUS_SUCCESS);
            break;
        }
        case EXP_COMMAND_SD_LIST_CHANNELS: {
            WriteStatus(buf, EXP_STATUS_BUSY);
            uint8_t *window = &buf[EXP_BUFFER_START_PAGE][EXP_BUFFER_START_ADDRESS];
            uint16_t count = 0;
            for (uint8_t i = 0; i < EXP_MAX_SD_CHANNELS && count < EXP_DIR_MAX_ENTRIES; i++) {
                if (!channelOpen[i]) continue;
                uint8_t *entry = window + 2 + (uint16_t)count * EXP_DIR_RECORD_SIZE;
                char label[EXP_DIR_NAME_LEN];
                uint8_t pos = 0;
                pos = (uint8_t)(pos + WriteDecimal((uint32_t)(i + 1), (uint8_t *)(label + pos)));
                if (pos < EXP_DIR_NAME_LEN) label[pos++] = ':';
                uint8_t j;
                for (j = 0; channelName[i][j] != 0 && pos < EXP_DIR_NAME_LEN; j++)
                    label[pos++] = channelName[i][j];
                uint8_t labelLen = pos;
                for (j = 0; j < EXP_DIR_NAME_LEN; j++)
                    entry[j] = (j < labelLen) ? (uint8_t)label[j] : ' ';
                for (j = 0; j < EXP_DIR_SIZE_TEXT_LEN; j++) (entry + EXP_DIR_NAME_LEN)[j] = ' ';
                for (j = 0; j < 4; j++) entry[EXP_DIR_NAME_LEN + EXP_DIR_SIZE_TEXT_LEN + j] = 0;
                count++;
            }
            window[0] = (uint8_t)(count >> 8);
            window[1] = (uint8_t)(count & 0xFF);
            {
                uint16_t summaryOffset = (uint16_t)(2 + (uint16_t)count * EXP_DIR_RECORD_SIZE);
                if (summaryOffset + EXP_DIR_SUMMARY_LEN <= 4095) {
                    char summary[16];
                    uint8_t pos = 0;
                    pos = (uint8_t)(pos + WriteDecimal((uint32_t)count, (uint8_t *)(summary + pos)));
                    summary[pos++] = ' ';
                    summary[pos++] = 'O';
                    summary[pos++] = 'P';
                    summary[pos++] = 'E';
                    summary[pos++] = 'N';
                    uint8_t k;
                    for (k = 0; k < EXP_DIR_SUMMARY_LEN; k++)
                        window[summaryOffset + k] = (k < pos) ? (uint8_t)summary[k] : ' ';
                }
            }
            WriteStatus(buf, EXP_STATUS_SUCCESS);
            break;
        }
        case EXP_COMMAND_SD_WRITE_VALUE: {
            WriteStatus(buf, EXP_STATUS_BUSY);
            uint8_t *window = &buf[EXP_BUFFER_START_PAGE][EXP_BUFFER_START_ADDRESS];
            uint8_t channel = window[0];
            if (channel < 1 || channel > EXP_MAX_SD_CHANNELS || !channelOpen[channel - 1]) {
                WriteStatus(buf, EXP_STATUS_ERROR);
                break;
            }
            uint8_t idx = channel - 1;
            uint8_t tag = window[1];
            uint16_t chunkLen;
            if (tag == 'N') chunkLen = 1 + 8;
            else if (tag == 'S') chunkLen = (uint16_t)(1 + 1 + window[2]);
            else {
                WriteStatus(buf, EXP_STATUS_ERROR);
                break;
            }
            SeekToEnd(&channelFile[idx]);
            UINT written = 0;
            f_write(&channelFile[idx], window + 1, chunkLen, &written);
            if (written != chunkLen) {
                WriteStatus(buf, EXP_STATUS_ERROR);
                break;
            }
            WriteStatus(buf, EXP_STATUS_SUCCESS);
            break;
        }
        case EXP_COMMAND_SD_CHANNEL_EOF: {
            /* SDEOF(n) (2026-09-30): nothing left to read past SD_READ_VALUE's
             * own position -- what makes its next read EOF. */
            uint8_t *window = &buf[EXP_BUFFER_START_PAGE][EXP_BUFFER_START_ADDRESS];
            uint8_t channel = window[0];
            if (channel < 1 || channel > EXP_MAX_SD_CHANNELS || !channelOpen[channel - 1]) {
                WriteStatus(buf, EXP_STATUS_ERROR);
                break;
            }
            window[0] = channelReadPos[channel - 1] >= (uint32_t)f_size(&channelFile[channel - 1]) ? 1 : 0;
            WriteStatus(buf, EXP_STATUS_SUCCESS);
            break;
        }
        case EXP_COMMAND_SD_READ_VALUE: {
            WriteStatus(buf, EXP_STATUS_BUSY);
            uint8_t *window = &buf[EXP_BUFFER_START_PAGE][EXP_BUFFER_START_ADDRESS];
            uint8_t channel = window[0];
            if (channel < 1 || channel > EXP_MAX_SD_CHANNELS || !channelOpen[channel - 1]) {
                WriteStatus(buf, EXP_STATUS_ERROR);
                break;
            }
            uint8_t idx = channel - 1;
            f_lseek(&channelFile[idx], channelReadPos[idx]);
            uint8_t tag;
            UINT got = 0;
            f_read(&channelFile[idx], &tag, 1, &got);
            if (got != 1) {
                WriteStatus(buf, EXP_STATUS_EOF);
                break;
            }
            uint16_t payloadLen;
            uint8_t lenByte = 0;
            if (tag == 'N') {
                payloadLen = 8;
            } else if (tag == 'S') {
                f_read(&channelFile[idx], &lenByte, 1, &got);
                if (got != 1) {
                    WriteStatus(buf, EXP_STATUS_EOF);
                    break;
                }
                payloadLen = lenByte;
            } else {
                WriteStatus(buf, EXP_STATUS_ERROR); /* corrupt file */
                break;
            }
            uint8_t payload[255];
            if (payloadLen > 0) {
                f_read(&channelFile[idx], payload, payloadLen, &got);
                if (got != payloadLen) {
                    WriteStatus(buf, EXP_STATUS_EOF);
                    break;
                }
            }
            uint16_t pos = 0;
            window[pos++] = tag;
            if (tag == 'S') window[pos++] = lenByte;
            for (uint16_t i = 0; i < payloadLen; i++) window[pos++] = payload[i];
            channelReadPos[idx] = (uint32_t)f_tell(&channelFile[idx]);
            WriteStatus(buf, EXP_STATUS_SUCCESS);
            break;
        }
        case EXP_COMMAND_SD_SKIP_VALUES: {
            WriteStatus(buf, EXP_STATUS_BUSY);
            uint8_t *window = &buf[EXP_BUFFER_START_PAGE][EXP_BUFFER_START_ADDRESS];
            uint8_t channel = window[0];
            if (channel < 1 || channel > EXP_MAX_SD_CHANNELS || !channelOpen[channel - 1]) {
                WriteStatus(buf, EXP_STATUS_ERROR);
                break;
            }
            uint8_t idx = channel - 1;
            uint16_t count = (uint16_t)window[1] * 256 + window[2];
            uint32_t pos = channelReadPos[idx];
            bool ok = true;
            for (uint16_t i = 0; i < count; i++) {
                f_lseek(&channelFile[idx], pos);
                uint8_t tag;
                UINT got = 0;
                f_read(&channelFile[idx], &tag, 1, &got);
                if (got != 1) {
                    ok = false;
                    break;
                }
                if (tag == 'N') {
                    pos += 1 + 8;
                } else if (tag == 'S') {
                    uint8_t lenByte = 0;
                    f_read(&channelFile[idx], &lenByte, 1, &got);
                    if (got != 1) {
                        ok = false;
                        break;
                    }
                    pos += (uint32_t)(1 + 1 + lenByte);
                } else {
                    ok = false;
                    break;
                }
            }
            if (!ok) {
                WriteStatus(buf, EXP_STATUS_ERROR);
                break;
            }
            channelReadPos[idx] = pos;
            WriteStatus(buf, EXP_STATUS_SUCCESS);
            break;
        }
        case EXP_COMMAND_VALIDATE_SD_NAME: {
            WriteStatus(buf, EXP_STATUS_BUSY);
            uint16_t nameLen = (uint16_t)buf[EXP_BUFFER_START_PAGE][EXP_BUFFER_START_ADDRESS] * 256 +
                                buf[EXP_BUFFER_START_PAGE][EXP_BUFFER_START_ADDRESS + 1];
            uint8_t *name = &buf[EXP_BUFFER_START_PAGE][EXP_BUFFER_START_ADDRESS + 2];
            uint8_t nameCount = 0, extCount = 0, dotSeen = 0, dotOnly = 1, valid = 1;
            uint16_t i;
            for (i = 0; i < nameLen && valid; i++) {
                uint8_t c = name[i];
                if (c >= 'a' && c <= 'z') c = (uint8_t)(c - 'a' + 'A');
                if (c == '/') {
                    nameCount = 0;
                    extCount = 0;
                    dotSeen = 0;
                    dotOnly = 1;
                } else if (c == '.') {
                    if (dotOnly) {
                        /* "." or ".." so far -- allow, don't touch counters */
                    } else if (dotSeen) {
                        valid = 0;
                    } else {
                        dotSeen = 1;
                    }
                } else {
                    dotOnly = 0;
                    if (!dotSeen) {
                        nameCount++;
                        if (nameCount > 8) valid = 0;
                    } else {
                        extCount++;
                        if (extCount > 3) valid = 0;
                    }
                }
                name[i] = c;
            }
            if (nameLen == 0) valid = 0;
            WriteStatus(buf, valid ? EXP_STATUS_SUCCESS : EXP_STATUS_ERROR);
            break;
        }
        case EXP_COMMAND_GET_SD_DF_TEXT: {
            WriteStatus(buf, EXP_STATUS_BUSY);
            uint32_t total, free_;
            GetVolumeSpace(&total, &free_);
            uint8_t text[32];
            uint8_t pos = 0;
            pos = (uint8_t)(pos + FormatHumanBytes(free_, text + pos));
            text[pos++] = ' ';
            text[pos++] = 'F';
            text[pos++] = ' ';
            text[pos++] = '/';
            text[pos++] = ' ';
            pos = (uint8_t)(pos + FormatHumanBytes(total, text + pos));
            text[pos++] = ' ';
            text[pos++] = 'T';
            buf[EXP_SCRATCH_PAGE][0] = pos;
            for (uint8_t i = 0; i < pos; i++) buf[EXP_SCRATCH_PAGE][i + 1] = text[i];
            WriteStatus(buf, EXP_STATUS_SUCCESS);
            break;
        }
        case EXP_COMMAND_LIST_SD_DIR: {
            WriteStatus(buf, EXP_STATUS_BUSY);
            uint8_t *window = &buf[EXP_BUFFER_START_PAGE][EXP_BUFFER_START_ADDRESS];
            DIR dir;
            FILINFO fno;
            uint16_t count = 0;
            uint32_t totalBytes = 0;
            FRESULT fr = f_findfirst(&dir, &fno, "", "*");
            while (fr == FR_OK && fno.fname[0] != 0 && count < EXP_DIR_MAX_ENTRIES) {
                /* FatFs's own find functions never return "."/".." --
                 * unlike emFile, so this loop never sees them. */
                uint8_t *entry = window + 2 + (uint16_t)count * EXP_DIR_RECORD_SIZE;
                ConvertTildeToPlus(fno.fname);
                uint8_t nameLen = (uint8_t)strlen(fno.fname);
                bool isDir = (fno.fattrib & AM_DIR) != 0;
                if (nameLen > EXP_DIR_NAME_LEN) nameLen = EXP_DIR_NAME_LEN;
                for (uint8_t i = 0; i < EXP_DIR_NAME_LEN; i++)
                    entry[i] = (i < nameLen) ? (uint8_t)fno.fname[i] : ' ';
                if (isDir) {
                    static const char dirText[] = "<DIR>";
                    uint8_t dirTextLen = (uint8_t)(sizeof(dirText) - 1);
                    uint8_t j;
                    for (j = 0; j < EXP_DIR_SIZE_TEXT_LEN; j++) (entry + EXP_DIR_NAME_LEN)[j] = ' ';
                    for (j = 0; j < dirTextLen; j++)
                        (entry + EXP_DIR_NAME_LEN)[EXP_DIR_SIZE_TEXT_LEN - dirTextLen + j] =
                            (uint8_t)dirText[j];
                } else {
                    FormatSizeText((uint32_t)fno.fsize, entry + EXP_DIR_NAME_LEN,
                                    EXP_DIR_SIZE_TEXT_LEN);
                }
                {
                    uint32_t sizeValue = isDir ? 0 : (uint32_t)fno.fsize;
                    entry[EXP_DIR_NAME_LEN + EXP_DIR_SIZE_TEXT_LEN] = (uint8_t)(sizeValue >> 24);
                    entry[EXP_DIR_NAME_LEN + EXP_DIR_SIZE_TEXT_LEN + 1] = (uint8_t)(sizeValue >> 16);
                    entry[EXP_DIR_NAME_LEN + EXP_DIR_SIZE_TEXT_LEN + 2] = (uint8_t)(sizeValue >> 8);
                    entry[EXP_DIR_NAME_LEN + EXP_DIR_SIZE_TEXT_LEN + 3] = (uint8_t)(sizeValue);
                }
                if (!isDir) totalBytes += (uint32_t)fno.fsize;
                count++;
                fr = f_findnext(&dir, &fno);
            }
            f_closedir(&dir);
            window[0] = (uint8_t)(count >> 8);
            window[1] = (uint8_t)(count & 0xFF);
            if (fr != FR_OK && count == 0) {
                /* The directory couldn't be read at all (no card, card
                 * swapped and failed to re-initialise, not FAT-formatted,
                 * ...). Said in the summary line, which SDLS and the
                 * SDLOAD picker display as-is -- SD_LIST_INIT doesn't look
                 * at the status, so a plain ERROR would show stale window
                 * contents instead. Previously this case read as a valid,
                 * empty "0 FILES 0 BYTES" listing. */
                char text[EXP_DIR_SUMMARY_LEN + 1];
                if (fr == FR_NOT_READY) snprintf(text, sizeof(text), "NO SD CARD");
                else if (fr == FR_NO_FILESYSTEM) snprintf(text, sizeof(text), "SD CARD NOT FORMATTED");
                else snprintf(text, sizeof(text), "SD CARD ERROR %d", (int)fr);
                uint8_t len = (uint8_t)strlen(text);
                for (uint8_t i = 0; i < EXP_DIR_SUMMARY_LEN; i++)
                    window[2 + i] = (i < len) ? (uint8_t)text[i] : ' ';
                WriteStatus(buf, EXP_STATUS_SUCCESS);
                break;
            }
            {
                uint16_t summaryOffset = (uint16_t)(2 + (uint16_t)count * EXP_DIR_RECORD_SIZE);
                if (summaryOffset + EXP_DIR_SUMMARY_LEN <= 4095) {
                    /* No GetVolumeSpace() here -- see FormatSummaryLineNoFreeSpace()'s
                     * own comment for why free space is left out of SDLS's summary
                     * line on this board. Use SDDF for that. */
                    FormatSummaryLineNoFreeSpace(count, totalBytes, window + summaryOffset,
                                                  EXP_DIR_SUMMARY_LEN);
                }
            }
            WriteStatus(buf, EXP_STATUS_SUCCESS);
            break;
        }
        case EXP_COMMAND_CLEAR_STATUS: {
            WriteStatus(buf, EXP_STATUS_READY);
            break;
        }
        case EXP_COMMAND_KEYWORD:
        case EXP_COMMAND_KEYWORD_CONTINUE: {
            /* Keyword executor -- see keywords.h / pc_exp.h. */
            if (req == EXP_COMMAND_KEYWORD) RestoreWindowCode();
            WriteStatus(buf, kw_command(req, &buf[0][0], RunNestedCommand, buf));
            break;
        }
        case EXP_COMMAND_FN_BLSTAT:
        case EXP_COMMAND_FN_SDEOF:
        case EXP_COMMAND_FN_WFSTAT:
            /* A keyword used as a BASIC function (2026-09-29). The reply
             * says whether a keyword is running (kw_function(), pc_exp.h);
             * if none is, rom.asm's BLSTAT_FN sends DONE itself once it has
             * read the value. Requesting sleep here instead (the first
             * version) let a STAGE RAM MCU go DORMANT before the ROM had
             * read the status and the value: ERROR 1 (2026-09-30). */
            WriteStatus(buf, kw_function(req, &buf[0][0], RunNestedCommand, buf));
            break;
        case EXP_COMMAND_CONFIG_GET:
        case EXP_COMMAND_CONFIG_SET: {
            /* MCONF -- see mcu_config.h. */
            uint8_t *w = &buf[EXP_BUFFER_START_PAGE][EXP_BUFFER_START_ADDRESS];
            bool ok = w[0] < MCU_CONFIG_COUNT;
            if (ok && req == EXP_COMMAND_CONFIG_SET) {
                uint16_t value = (uint16_t)((w[1] << 8) | w[2]);
                if (w[0] == MCU_CONFIG_LOGSIZE) {
                    /* whole 4K sectors, between the minimum and what fits */
                    ok = value >= MCU_LOG_MIN_SIZE_KB && value <= mcu_log_max_size_kb() && value % 4 == 0;
                    if (ok && value != mcu_config_get(MCU_CONFIG_LOGSIZE)) {
                        ok = mcu_config_set(w[0], value);
                        mcu_log_resize();
                    }
                } else {
                    ok = mcu_config_set(w[0], value);
                }
            } else if (ok) {
                uint16_t v = mcu_config_get(w[0]);
                w[1] = (uint8_t)(v >> 8);
                w[2] = (uint8_t)v;
            }
            WriteStatus(buf, ok ? EXP_STATUS_SUCCESS : EXP_STATUS_ERROR);
            break;
        }
        case EXP_COMMAND_CONFIG_HOSTNAME_GET:
        case EXP_COMMAND_CONFIG_HOSTNAME_SET: {
            /* MCONF HOSTNAME -- see mcu_config.h. */
            uint8_t *w = &buf[EXP_BUFFER_START_PAGE][EXP_BUFFER_START_ADDRESS];
            bool ok = true;
            if (req == EXP_COMMAND_CONFIG_HOSTNAME_SET) {
                ok = mcu_config_set_hostname((const char *)w + 1, w[0]);
            } else {
                const char *h = mcu_config_get_hostname();
                w[0] = (uint8_t)strlen(h);
                memcpy(w + 1, h, w[0]);
            }
            WriteStatus(buf, ok ? EXP_STATUS_SUCCESS : EXP_STATUS_ERROR);
            break;
        }
        case EXP_COMMAND_STORE_ERASE:
        case EXP_COMMAND_STORE_WRITE:
        case EXP_COMMAND_STORE_READ: {
            /* FNSAVE/FNLOAD/STSAVE/STLOAD -- see mcu_store.h. */
            const uint8_t *p = &buf[0][0] + EXP_STORE_PARAMS;
            uint8_t *data = &buf[EXP_BUFFER_START_PAGE][EXP_BUFFER_START_ADDRESS];
            uint32_t offset = (uint32_t)((p[1] << 8) | p[2]);
            uint32_t len = (uint32_t)((p[3] << 8) | p[4]);
            bool ok = false;
            if (len > EXP_MAX_TRANSFER_LEN * 2) len = 0; /* the window's payload area */
            if (p[0] > EXP_STORE_SLOT_STATE) {
                /* the Link's keys (slot 2) never reach the PC-1500's side */
            } else if (req == EXP_COMMAND_STORE_ERASE) ok = mcu_store_erase(p[0]);
            else if (len == 0) ok = false;
            else if (req == EXP_COMMAND_STORE_WRITE) ok = mcu_store_write(p[0], offset, data, len);
            else ok = mcu_store_read(p[0], offset, data, len);
            WriteStatus(buf, ok ? EXP_STATUS_SUCCESS : EXP_STATUS_ERROR);
            break;
        }
        case EXP_COMMAND_KBD_PAIR:
        case EXP_COMMAND_KBD_STATUS:
        case EXP_COMMAND_KBD_STOP:
        case EXP_COMMAND_KBD_FORGET:
            WriteStatus(buf, kbd_host_command(req, &buf[EXP_BUFFER_START_PAGE][EXP_BUFFER_START_ADDRESS]));
            break;
        case EXP_COMMAND_KBD_INSTALL: {
            /* The external keyboard's driver (2026-10-04, MCONF BLKBD): the
             * boot hook's copy of ROM1's wait loop, checked and patched into
             * the ROM image (pages 8-31) -- see kbd_seq.h. Sent by the boot
             * hook, and by BLKBD after a pairing (keywords.c kbd_arm()), only
             * when the ROM being served lacks it -- so a staged copy doesn't
             * have it, and is out of date now. */
            uint32_t crc;
            kbd_loop_result_t r =
                kbd_loop_install(&buf[EXP_BUFFER_START_PAGE][EXP_BUFFER_START_ADDRESS], &buf[8][0], 24u * 256u, &crc);
            if (r == KBD_LOOP_OK) {
                romStagedVerified = false;
                mcu_log_info("KBD loop installed");
            } else if (r == KBD_LOOP_NO_HOOK) {
                mcu_log_error("KBD: ROM hook unusable"); /* an older PC-1500 ROM, kbd_seq.h */
            } else if (r == KBD_LOOP_UNKNOWN_ROM) {      /* the loop's CRC, to identify it */
                static const char hex[] = "0123456789ABCDEF";
                char msg[] = "KBD: ROM CRC ........";
                for (int i = 0; i < 8; i++) msg[sizeof msg - 9 + i] = hex[(crc >> (28 - 4 * i)) & 15u];
                mcu_log_error(msg);
            } else {
                mcu_log_error("KBD: bad ROM layout");
            }
            WriteStatus(buf, r == KBD_LOOP_OK ? EXP_STATUS_SUCCESS : EXP_STATUS_ERROR);
            break;
        }
        case EXP_COMMAND_DONE: {
            /* End of an expansion keyword -- see the "STAGE RAM sleep"
             * section's header. The flag is set BEFORE the final status, so
             * it's already visible once the ROM's EC_DONE poll sees
             * SUCCESS; core0 then sleeps unless another command has come in
             * first (forwarding one cancels the request). In MCU mode this
             * is a no-op. */
            g_sleep_requested_us = time_us_32();
            g_sleep_requested = romStagedVerified;
            WriteStatus(buf, EXP_STATUS_SUCCESS);
            break;
        }
        case EXP_COMMAND_CREATE_SD_FILE: {
            WriteStatus(buf, EXP_STATUS_BUSY);
            uint16_t fileNameLen = buf[EXP_BUFFER_START_PAGE][EXP_BUFFER_START_ADDRESS] * 256 +
                                    buf[EXP_BUFFER_START_PAGE][EXP_BUFFER_START_ADDRESS + 1];
            if (fileNameLen == 0 || fileNameLen > EXP_PATH_ARG_LEN) {
                WriteStatus(buf, EXP_STATUS_ERROR);
                break;
            }
            char fileName[EXP_PATH_ARG_LEN + 1];
            StringFromBuffer(buf, EXP_BUFFER_START_PAGE, EXP_BUFFER_START_ADDRESS + 2, fileNameLen,
                              fileName);
            char fsName[EXP_PATH_ARG_LEN + 1];
            PrepareFsName(fileName, fsName, sizeof(fsName));
            currentFileOpen = f_open(&currentFile, fsName, FA_CREATE_ALWAYS | FA_WRITE) == FR_OK;
            if (!currentFileOpen) {
                WriteStatus(buf, EXP_STATUS_ERROR);
            } else {
                currentFileStatus = EXP_SD_FILE_STATUS_OPEN_WRITE;
                strncpy(currentFileName, fileName, sizeof(currentFileName) - 1);
                currentFileName[sizeof(currentFileName) - 1] = 0;
                WriteStatus(buf, EXP_STATUS_SUCCESS);
            }
            break;
        }
        case EXP_COMMAND_OPEN_SD_FILE_READ: {
            WriteStatus(buf, EXP_STATUS_BUSY);
            uint16_t readNameLen = buf[EXP_BUFFER_START_PAGE][EXP_BUFFER_START_ADDRESS] * 256 +
                                    buf[EXP_BUFFER_START_PAGE][EXP_BUFFER_START_ADDRESS + 1];
            if (readNameLen == 0 || readNameLen > EXP_PATH_ARG_LEN) {
                WriteStatus(buf, EXP_STATUS_ERROR);
                break;
            }
            char readFileName[EXP_PATH_ARG_LEN + 1];
            StringFromBuffer(buf, EXP_BUFFER_START_PAGE, EXP_BUFFER_START_ADDRESS + 2, readNameLen,
                              readFileName);
            char readFsName[EXP_PATH_ARG_LEN + 1];
            PrepareFsName(readFileName, readFsName, sizeof(readFsName));
            currentFileOpen = f_open(&currentFile, readFsName, FA_READ) == FR_OK;
            if (!currentFileOpen) {
                WriteStatus(buf, EXP_STATUS_ERROR);
            } else {
                currentFileStatus = EXP_SD_FILE_STATUS_OPEN_READ;
                strncpy(currentFileName, readFileName, sizeof(currentFileName) - 1);
                currentFileName[sizeof(currentFileName) - 1] = 0;
                WriteStatus(buf, EXP_STATUS_SUCCESS);
            }
            break;
        }
        case EXP_COMMAND_GET_SD_FILE_STATUS: {
            WriteStatus(buf, EXP_STATUS_BUSY);
            buf[EXP_BUFFER_START_PAGE][EXP_BUFFER_START_ADDRESS] = currentFileStatus;
            WriteStatus(buf, EXP_STATUS_SUCCESS);
            break;
        }
        case EXP_COMMAND_BLE_SCAN:
        case EXP_COMMAND_BLE_CONNECT:
        case EXP_COMMAND_BLE_CONNECT_NAME:
        case EXP_COMMAND_BLE_DISCONNECT:
        case EXP_COMMAND_BLE_TEXT:
        case EXP_COMMAND_BLE_FILE_PUT:
        case EXP_COMMAND_BLE_FILE_GET:
        case EXP_COMMAND_BLE_ADVERTISE:
        case EXP_COMMAND_BLE_STATUS:
        case EXP_COMMAND_BLE_OFFER:
        case EXP_COMMAND_BLE_WITHDRAW:
        case EXP_COMMAND_BLE_OFFER_GET:
        case EXP_COMMAND_BLE_ANSWER:
        case EXP_COMMAND_BLE_SEND:
        case EXP_COMMAND_BLE_DATA_WRITE:
        case EXP_COMMAND_BLE_DATA_READ:
        case EXP_COMMAND_BLE_DATA_CLOSE:
        case EXP_COMMAND_BLE_MSG_SEND:
        case EXP_COMMAND_BLE_MSG_WAIT:
        case EXP_COMMAND_BLE_MSG_RECV:
        case EXP_COMMAND_BLE_MSG_COUNT:
        case EXP_COMMAND_BLE_PLOT:
        case EXP_COMMAND_BLE_PAIR_BEGIN:
        case EXP_COMMAND_BLE_PAIR_CONFIRM:
        case EXP_COMMAND_BLE_PAIR_ANSWER:
        case EXP_COMMAND_BLE_UNPAIR:
            /* BL* keywords (nested, from keywords.c) -- ble_link.h */
            WriteStatus(buf, ble_link_command(req, &buf[0][0]));
            break;
        case EXP_COMMAND_WIFI_SCAN:
        case EXP_COMMAND_WIFI_CONNECT:
        case EXP_COMMAND_WIFI_CONNECT_NAME:
        case EXP_COMMAND_WIFI_DISCONNECT:
        case EXP_COMMAND_WIFI_STATUS:
        case EXP_COMMAND_WIFI_FORGET:
            /* WF* keywords (nested, from keywords.c) -- wifi_link.h */
            WriteStatus(buf, wifi_link_command(req, &buf[0][0]));
            break;
        case EXP_COMMAND_SSH_OPEN:
        case EXP_COMMAND_SSH_STEP:
        case EXP_COMMAND_SSH_ANSWER:
        case EXP_COMMAND_SSH_PASSWORD:
        case EXP_COMMAND_SSH_TERM:
        case EXP_COMMAND_SSH_CLOSE:
        case EXP_COMMAND_SSH_KEY:
        case EXP_COMMAND_SSH_FORGET:
            /* SSH (nested, from keywords.c, 2026-10-07) -- ssh_session.h */
            WriteStatus(buf, ssh_session_command(req, &buf[0][0]));
            break;
        case EXP_COMMAND_HIST_ADD:
        case EXP_COMMAND_HIST_BEGIN:
            /* the command history (from the keyboard driver, 2026-10-07) -- history_session.h */
            WriteStatus(buf, history_session_command(req, &buf[0][0]));
            break;
        case EXP_COMMAND_PING_START:
        case EXP_COMMAND_PING_ROUND:
            /* WFPING (nested, from keywords.c, 2026-10-07) -- net_ping.h */
            WriteStatus(buf, net_ping_command(req, &buf[0][0]));
            break;
        case EXP_COMMAND_TIME_GET:
        case EXP_COMMAND_CONFIG_TZ_GET:
        case EXP_COMMAND_CONFIG_TZ_SET:
            /* the clock from WFCON/BLCON, MCONF TZ (nested, from keywords.c, 2026-10-08) -- time_sync.h */
            WriteStatus(buf, time_sync_command(req, &buf[EXP_BUFFER_START_PAGE][EXP_BUFFER_START_ADDRESS]));
            break;
        case EXP_COMMAND_WRITE_TO_SD_FILE: {
            if (basic_xlate_mode() != BASIC_XLATE_OFF) { /* a BASIC save: CE-150 codes (basic_xlate.h) */
                uint16_t n = (buf[EXP_LENGTH_PORT_PAGE][EXP_LENGTH_PORT_ADDRESS] << 8) +
                             buf[EXP_LENGTH_PORT_PAGE][EXP_LENGTH_PORT_ADDRESS + 1];
                n = basic_xlate_write(&buf[EXP_BUFFER_START_PAGE][EXP_BUFFER_START_ADDRESS], n);
                buf[EXP_LENGTH_PORT_PAGE][EXP_LENGTH_PORT_ADDRESS] = (uint8_t)(n >> 8);
                buf[EXP_LENGTH_PORT_PAGE][EXP_LENGTH_PORT_ADDRESS + 1] = (uint8_t)n;
                if (n == 0) { /* all of it held back for the next chunk */
                    WriteStatus(buf, EXP_STATUS_SUCCESS);
                    break;
                }
            }
            if (ble_link_transfer_open()) { /* BLSAVE: to the BLE peer */
                WriteStatus(buf, ble_link_command(req, &buf[0][0]));
                break;
            }
            if (!currentFileOpen || currentFileStatus != EXP_SD_FILE_STATUS_OPEN_WRITE) break;
            WriteStatus(buf, EXP_STATUS_BUSY);
            uint16_t dataLen = (buf[EXP_LENGTH_PORT_PAGE][EXP_LENGTH_PORT_ADDRESS] << 8) +
                                buf[EXP_LENGTH_PORT_PAGE][EXP_LENGTH_PORT_ADDRESS + 1];
            if (dataLen == 0) {
                WriteStatus(buf, EXP_STATUS_ERROR);
                break;
            }
            const uint8_t *src = &buf[EXP_BUFFER_START_PAGE][EXP_BUFFER_START_ADDRESS];
            UINT dataWritten = 0;
            f_write(&currentFile, src, dataLen, &dataWritten);
            if (dataWritten == dataLen) {
                WriteStatus(buf, EXP_STATUS_SUCCESS);
                fileEnd += dataLen;
            } else {
                WriteStatus(buf, EXP_STATUS_ERROR);
            }
            break;
        }
        case EXP_COMMAND_READ_FROM_SD_FILE: {
            if (ble_link_transfer_open()) { /* BLLOAD: from the BLE peer */
                uint8_t status = ble_link_command(req, &buf[0][0]);
                if (status == EXP_STATUS_SUCCESS) TranslateRead(buf);
                WriteStatus(buf, status);
                break;
            }
            if (!currentFileOpen || currentFileStatus != EXP_SD_FILE_STATUS_OPEN_READ) {
                WriteStatus(buf, EXP_STATUS_ERROR);
                break;
            }
            WriteStatus(buf, EXP_STATUS_BUSY);
            uint16_t requestLen = (buf[EXP_LENGTH_PORT_PAGE][EXP_LENGTH_PORT_ADDRESS] << 8) +
                                   buf[EXP_LENGTH_PORT_PAGE][EXP_LENGTH_PORT_ADDRESS + 1];
            if (requestLen == 0 || requestLen > EXP_MAX_TRANSFER_LEN) {
                WriteStatus(buf, EXP_STATUS_ERROR);
                break;
            }
            uint8_t *readDest = &buf[EXP_BUFFER_START_PAGE][EXP_BUFFER_START_ADDRESS];
            UINT bytesRead = 0;
            f_read(&currentFile, readDest, requestLen, &bytesRead);
            buf[EXP_LENGTH_PORT_PAGE][EXP_LENGTH_PORT_ADDRESS] = (uint8_t)(bytesRead >> 8);
            buf[EXP_LENGTH_PORT_PAGE][EXP_LENGTH_PORT_ADDRESS + 1] = (uint8_t)(bytesRead & 255);
            TranslateRead(buf);
            WriteStatus(buf, EXP_STATUS_SUCCESS);
            break;
        }
        case EXP_COMMAND_CLOSE_SD_FILE: {
            if (basic_xlate_mode() == BASIC_XLATE_SAVE) { /* a byte still held back: write it first */
                uint8_t *d = &buf[EXP_BUFFER_START_PAGE][EXP_BUFFER_START_ADDRESS];
                if (basic_xlate_flush(d)) {
                    buf[EXP_LENGTH_PORT_PAGE][EXP_LENGTH_PORT_ADDRESS] = 0;
                    buf[EXP_LENGTH_PORT_PAGE][EXP_LENGTH_PORT_ADDRESS + 1] = 1;
                    if (ble_link_transfer_open()) {
                        ble_link_command(EXP_COMMAND_WRITE_TO_SD_FILE, &buf[0][0]);
                    } else if (currentFileOpen) {
                        UINT written = 0;
                        f_write(&currentFile, d, 1, &written);
                        fileEnd += written;
                    }
                }
            }
            basic_xlate_end();
            if (ble_link_transfer_open()) { /* SUCCESS only if the whole file moved */
                WriteStatus(buf, ble_link_command(req, &buf[0][0]));
                break;
            }
            if (!currentFileOpen || currentFileStatus == EXP_SD_FILE_STATUS_CLOSED) break;
            WriteStatus(buf, EXP_STATUS_BUSY);
            FRESULT result = f_close(&currentFile);
            if (result == FR_OK) {
                currentFileOpen = false;
                currentFileStatus = EXP_SD_FILE_STATUS_CLOSED;
                WriteStatus(buf, EXP_STATUS_SUCCESS);
                LongToBuffer(buf, EXP_BUFFER_START_PAGE, EXP_BUFFER_START_ADDRESS, fileEnd);
                fileEnd = 0;
            } else {
                WriteStatus(buf, EXP_STATUS_ERROR);
                LongToBuffer(buf, EXP_BUFFER_START_PAGE, EXP_BUFFER_START_ADDRESS, (uint32_t)result);
            }
            break;
        }
        case EXP_COMMAND_FORMAT_SD_CARD: {
            WriteStatus(buf, EXP_STATUS_BUSY);
            uint16_t volumeNameLen = buf[EXP_BUFFER_START_PAGE][EXP_BUFFER_START_ADDRESS] * 256 +
                                      buf[EXP_BUFFER_START_PAGE][EXP_BUFFER_START_ADDRESS + 1];
            if (volumeNameLen == 0) {
                WriteStatus(buf, EXP_STATUS_ERROR);
                break;
            }
            char volumeName[EXP_PATH_ARG_LEN + 1];
            if (volumeNameLen > EXP_PATH_ARG_LEN) volumeNameLen = EXP_PATH_ARG_LEN;
            StringFromBuffer(buf, EXP_BUFFER_START_PAGE, EXP_BUFFER_START_ADDRESS + 2,
                              volumeNameLen, volumeName);
            static uint8_t mkfsWork[FF_MAX_SS];
            MKFS_PARM opt = {.fmt = FM_ANY, .n_fat = 0, .align = 0, .n_root = 0, .au_size = 0};
            WriteStatus(buf, f_mkfs(volumeName, &opt, mkfsWork, sizeof(mkfsWork)) == FR_OK
                                  ? EXP_STATUS_SUCCESS
                                  : EXP_STATUS_ERROR);
            break;
        }
        case EXP_COMMAND_TEST_COPY_STRING: {
            WriteStatus(buf, EXP_STATUS_BUSY);
            uint16_t dataLen = buf[EXP_BUFFER_START_PAGE][EXP_BUFFER_START_ADDRESS] * 256 +
                                buf[EXP_BUFFER_START_PAGE][EXP_BUFFER_START_ADDRESS + 1];
            if (dataLen == 0 || dataLen > 254) {
                WriteStatus(buf, EXP_STATUS_ERROR);
                break;
            }
            char testString[255];
            StringFromBuffer(buf, EXP_BUFFER_START_PAGE, EXP_BUFFER_START_ADDRESS + 2, dataLen,
                              testString);
            for (uint16_t i = 0; i < dataLen; i++) buf[4][i + 1] = testString[i];
            buf[4][0] = (uint8_t)dataLen;
            WriteStatus(buf, EXP_STATUS_SUCCESS);
            break;
        }
        default: {
            WriteStatus(buf, EXP_STATUS_NOT_IMPLEMENTED);
            break;
        }
    }
}

/* ============================================================
 * Bus loop -- ported from main()'s for(;;) in main.c, restructured
 * around the GreenPAK's two combined trigger lines (see board_pins.h)
 * instead of separately-sampled CS/RW/OE pins.
 * ============================================================ */

static void InitGpio(void) {
    for (int p = ADDR_PIN_BASE; p < ADDR_PIN_BASE + ADDR_PIN_COUNT; p++) {
        gpio_init(p);
        /* Pull-DOWN (2026-09-25, board owner's call) -- previously no
         * pull. Part of chasing a back-feed into the PC-1500's VCC rail
         * while the Pico is powered and the PC-1500 is off: removing the
         * data-line pull-ups cut LCD noise but not the feedback, so both
         * buses now pull toward GND instead. A few uA per pin while the
         * PC-1500 drives them, which the LH5801 overrides easily. */
        gpio_set_pulls(p, false, true);
    }
    for (int p = DATA_PIN_BASE; p < DATA_PIN_BASE + DATA_PIN_COUNT; p++) {
        gpio_init(p);
        /* Pull-DOWN (2026-09-25, board owner's call). History: pull-down
         * until U6 came off (2026-09-22), then pull-up, then briefly no
         * pull. The pull-up was dropped because 3.3V pulls on a bus wired
         * straight to the PC-1500 can back-feed its VCC rail through the
         * PC-1500 chips' input clamp diodes while the Pico is powered and
         * the PC-1500 is off (see the Q1/Vbus issue) -- removing it cut LCD
         * noise but not the VCC feedback, so this now matches the address
         * bus above.
         *
         * Side effect: while the MCU sleeps (STAGE RAM mode) the data
         * window reads 0x00 rather than 0xFF. EC_WAKE only accepts READY
         * (0x04), so that's safe; no status uses 0x00 either. */
        gpio_set_pulls(p, false, true);
    }
    gpio_init(PIN_TRIG_RD);
    gpio_set_pulls(PIN_TRIG_RD, false, false);
    gpio_init(PIN_TRIG_WR);
    gpio_set_pulls(PIN_TRIG_WR, false, false);
    /* Data pins start as inputs (Hi-Z) -- only driven while servicing a
     * read-trigger, see the loop below. Address/trigger pins are always
     * inputs from this chip's side. */
}

/* ============================================================
 * PIO-driven read-trigger path (2026-09-18) -- see read_serve.pio's own
 * header comment for the design. Replaces the software read-trigger
 * branch in monitor_run() below entirely: once running, reads are
 * answered by PIO+DMA in hardware, with no core involved. Write-trigger
 * handling is separately disabled for this phase (see monitor_run()'s own
 * comment) -- this is a deliberate, temporary split to validate the read
 * path in isolation (e.g. via repeated ECVER runs, which only exercise
 * ROM reads through the base ROM's own keyword-table walk) before
 * re-integrating writes.
 *
 * DMA chaining uses OneROM's own documented "continuous" mode (both
 * channels free-running with an effectively-infinite transfer count,
 * paced by the SAME dreq -- the address SM's own RX-FIFO-has-data signal
 * -- rather than an explicit re-trigger). A first attempt used a
 * single-shot "trigger alias" scheme with channel A configured to
 * CHAIN_TO itself, on the mistaken assumption that would make it
 * self-retrigger after each transfer -- confirmed against the actual
 * RP2350 register documentation (hardware/regs/dma.h) that CHAIN_TO set
 * to a channel's own number specifically means "chaining disabled", not
 * self-retrigger. That bug meant channel A fired exactly once, ever, then
 * silently stopped -- starving read_serve's TX FIFO after its first byte
 * and leaving that state machine permanently stalled on its next `out
 * pins, 8`, waiting for an autopull refill that could never arrive again.
 * Confirmed live on real hardware as a hang (ECVER) and an unexplained
 * audible "clicking" from the MCU on a second attempt -- reverted to the
 * last known-good checkpoint before diagnosing this from the datasheet,
 * then reapplied here with the corrected continuous-mode design. */

static uint dma_addr_relay, dma_data_fetch;
static uint sm_addr_capture, sm_read_serve;
static uint offset_addr, offset_read; /* kept for BusServeRestart() */

/* Loads addr_capture's X with the fixed buffer-base prefix -- once at
 * setup, and again by BusServeRestart() after DORMANT. */
static void PreloadReadServeRegs(void) {
    uint32_t prefix = (uint32_t)(uintptr_t)buffer >> ADDR_PIN_COUNT;
    pio_sm_put_blocking(pio0, sm_addr_capture, prefix);
    pio_sm_exec_wait_blocking(pio0, sm_addr_capture, pio_encode_pull(false, true));
    pio_sm_exec_wait_blocking(pio0, sm_addr_capture, pio_encode_mov(pio_x, pio_osr));
}

static void SetupReadServePio(void) {
    /* Data pins need to be owned by PIO0 to actually be driven by it;
     * address/trigger pins don't -- PIO's IN/WAIT/JMP-on-pin instructions
     * read the GPIO input synchronizer directly regardless of which
     * peripheral has function-select ownership, so InitGpio()'s existing
     * plain-GPIO configuration for those is left alone. */
    for (int p = DATA_PIN_BASE; p < DATA_PIN_BASE + DATA_PIN_COUNT; p++) {
        pio_gpio_init(pio0, p);
    }
    pio_sm_set_consecutive_pindirs(pio0, 0, DATA_PIN_BASE, DATA_PIN_COUNT, false); /* start as inputs */

    /* 2026-09-22: reverted to this two-SM, DMA-chained design (board
     * owner's own call) after a same-day detour into single-SM redesigns
     * (first still DMA-chained, then fully CPU-serviced) chasing STAGE
     * DEBUG's read corruption -- see read_serve.pio's own header note for
     * the full account. That investigation eventually traced the
     * corruption to U6 (TXS0108EPWR), an electrical level-shifter issue
     * physically removed from the board, not anything in this file's own
     * design. This is the best-performing version prior to that detour,
     * restored as the baseline to retest against a bus no longer fighting
     * the level shifter's own retrigger behavior. The LED-handling and
     * I2C-read-timeout fixes made earlier the same day (elsewhere in this
     * file, and in greenpak_i2c.c) are kept -- independent of which
     * read-serve design is active. */
    sm_addr_capture = pio_claim_unused_sm(pio0, true);
    sm_read_serve = pio_claim_unused_sm(pio0, true);
    offset_addr = pio_add_program(pio0, &addr_capture_program);
    offset_read = pio_add_program(pio0, &read_serve_program);

    /* addr_capture: on each rising edge of PIN_TRIG_RD, shifts (fixed
     * buffer-base prefix) then (live 13-bit address bus) into a 32-bit
     * ISR, autopushed to RX FIFO -- see buffer[]'s own 8192-byte-alignment
     * comment for why this produces a correct, ready-to-use absolute
     * address, and read_serve.pio's own header comment for why capture is
     * gated on the trigger (edge-gated redesign, 2026-09-18). */
    pio_sm_config c_addr = addr_capture_program_get_default_config(offset_addr);
    sm_config_set_in_pins(&c_addr, ADDR_PIN_BASE);
    sm_config_set_jmp_pin(&c_addr, PIN_TRIG_RD);   /* gates capture on the
                                                       read trigger; see
                                                       read_serve.pio's
                                                       header */
    sm_config_set_in_shift(&c_addr, false /* shift left */, true /* autopush */, 32);
    /* Full speed, undivided (~150MHz) clock -- an earlier /125 divider
     * caused this SM to almost always sample the address bus during its
     * idle/rest state instead of the brief live-address window a real
     * LH5801 read cycle presents (every live address bit tested came back
     * 0 on real hardware). Now that capture is also edge-gated on
     * PIN_TRIG_RD (see read_serve.pio's header and sm_config_set_jmp_pin
     * above), full speed additionally matters so the wait_high/wait_low
     * poll loop notices the trigger's rising and falling edges promptly
     * enough to finish capturing well inside the trigger's own asserted
     * window, rather than for the "flood of DMA transfers" reason this
     * divider was originally about -- that concern no longer applies at
     * all now that a transfer only ever happens once per real access. */
    sm_config_set_clkdiv(&c_addr, 1.0f);
    pio_sm_init(pio0, sm_addr_capture, offset_addr, &c_addr);

    /* Preload X with the fixed prefix (buffer's own base address's high
     * 19 bits) -- matches OneROM's own setup-time PULL_BLOCK/MOV X,OSR
     * sequence, done once before the SM starts running. */
    PreloadReadServeRegs();

    /* read_serve: drives the data pins from whatever byte the DMA chain
     * below has staged in this SM's TX FIFO, only while PIN_TRIG_RD is
     * asserted. */
    pio_sm_config c_read = read_serve_program_get_default_config(offset_read);
    sm_config_set_out_pins(&c_read, DATA_PIN_BASE, DATA_PIN_COUNT);
    /* shift RIGHT (2026-09-18, corrected from an initial wrong guess of
     * shift-left): an 8-bit-sized DMA write into this SM's 32-bit TX FIFO
     * register places the byte in the low byte lane (bits 7:0). Shift-right
     * is also the SDK's own default convention (pio_get_default_sm_config())
     * for exactly this reason -- OUT consumes the low bits first, matching
     * where the DMA-written byte actually landed. Shift-left would instead
     * read the upper, never-written (zero) bits -- confirmed live on real
     * hardware: every PEEK returned 0 with shift-left, a clean, non-random
     * failure consistent with this exact mistake (not a hang or garbage,
     * since the state machine was otherwise running correctly after fixing
     * the earlier chain_to bug). */
    sm_config_set_out_shift(&c_read, true, true /* autopull */, 8);
    pio_sm_init(pio0, sm_read_serve, offset_read, &c_read);

    /* DMA chain -- around RP2350's TRIGGER_SELF transfer-count mode plus
     * channel B's own triggering address alias.
     *
     * RP2350's own transfer_count register has a MODE field (top 4 bits,
     * confirmed via hardware/regs/dma.h -- NOT present on RP2040, where
     * the whole register is a plain 32-bit count): MODE 0x1
     * (TRIGGER_SELF) makes a single-element transfer automatically
     * re-trigger itself once it completes -- the datasheet's own words,
     * "useful for e.g. an endless ring-buffer DMA".
     *   - Channel A: ONE element per transfer (COUNT=1, MODE=TRIGGER_SELF),
     *     paced by addr_capture's RX dreq -- each time a new address word
     *     arrives, reads it and writes it to channel B's *triggering*
     *     al3_read_addr_trig alias (setting the address AND immediately
     *     starting channel B's own transfer as one hardware-native
     *     action), then automatically re-arms itself for the next word.
     *   - Channel B: ONE element per transfer (COUNT=1, MODE=NORMAL,
     *     chain_to left at its default/self, i.e. no auto-chaining --
     *     deliberate, since it should only ever run when channel A's
     *     al3 write above triggers it, never on its own), no dreq at all
     *     needed (unpaced -- once triggered, it just runs immediately):
     *     reads one byte from whatever address channel A most recently
     *     set and hands it to read_serve's TX FIFO. Configured but NOT
     *     triggered at setup time (trigger=false) -- its first real
     *     transfer comes from channel A's first al3 write, not from
     *     this initial configuration call. */
    dma_addr_relay = dma_claim_unused_channel(true);
    dma_data_fetch = dma_claim_unused_channel(true);

    uint addr_capture_dreq = pio_get_dreq(pio0, sm_addr_capture, false /* rx */);

    dma_channel_config ca = dma_channel_get_default_config(dma_addr_relay);
    channel_config_set_transfer_data_size(&ca, DMA_SIZE_32);
    channel_config_set_read_increment(&ca, false);
    channel_config_set_write_increment(&ca, false);
    channel_config_set_dreq(&ca, addr_capture_dreq);
    dma_channel_configure(
        dma_addr_relay,
        &ca,
        &dma_channel_hw_addr(dma_data_fetch)->al3_read_addr_trig, /* TRIGGERING alias -- this write both
                                                                       sets channel B's read address AND
                                                                       starts its transfer */
        &pio0->rxf[sm_addr_capture],
        (1u << 28) | 1u, /* MODE=0x1 (TRIGGER_SELF, bits 31:28), COUNT=1 (bits 27:0) */
        true
    );

    dma_channel_config cb = dma_channel_get_default_config(dma_data_fetch);
    channel_config_set_transfer_data_size(&cb, DMA_SIZE_8);
    channel_config_set_read_increment(&cb, false);
    channel_config_set_write_increment(&cb, false);
    /* No dreq set -- default unpaced (DREQ_FORCE), correct here since
       channel B should run immediately, at full speed, the instant
       channel A's al3 write above triggers it, not wait on anything
       further. */
    dma_channel_configure(
        dma_data_fetch,
        &cb,
        &pio0->txf[sm_read_serve],
        buffer, /* placeholder initial address -- channel A's first al3 write overwrites this
                    before it's ever meaningfully read */
        1u, /* MODE=0x0 (NORMAL), COUNT=1 -- one element per external trigger from channel A */
        false /* do NOT trigger here -- channel A's first al3 write is what starts channel B */
    );

    pio_sm_set_enabled(pio0, sm_addr_capture, true);
    pio_sm_set_enabled(pio0, sm_read_serve, true);
}

/* ============================================================
 * PIO-driven write-trigger path (2026-09-19) -- see write_serve.pio's own
 * header comment for the full design. Four state machines on pio1 (left
 * entirely separate from pio0's own read-path SMs above, which are
 * already validated and untouched): trigger_detect_wr is the sole
 * observer of PIN_TRIG_WR; addr_capture_wr captures the live address and
 * decides ordinary-write vs. command-dispatch; data_capture_wr_ordinary
 * and data_capture_wr_dispatch each capture the live data byte for their
 * respective case. Only the ordinary case ever reaches buffer[] via DMA
 * -- the dispatch case deliberately never does, since pc_exp.h's
 * EXP_COMMAND_* values numerically collide with EXP_STATUS_BUSY/SUCCESS/
 * EOF (e.g. EXP_COMMAND_CREATE_SD_FILE=2 == EXP_STATUS_SUCCESS=2), so a
 * raw, not-yet-interpreted command byte must never be allowed to sit in
 * buffer[EXP_INSTRUCTION_PAGE][EXP_INSTRUCTION_ADDRESS] even transiently
 * -- only software (see monitor_run()'s own dispatch poll below) may
 * ever write real EXP_STATUS_* values there.
 *
 * 2026-09-22: reverted to this four-SM, DMA-chained design (board owner's
 * own call) after a same-day detour into a single-SM, CPU-serviced
 * redesign -- see read_serve.pio's own history note (same day, same
 * reasoning) for the full account; that investigation traced the read
 * corruption motivating both detours to U6 (TXS0108EPWR), an electrical
 * issue physically removed from the board, unrelated to either read or
 * write path design. This is the best-performing version prior to that
 * detour. */

/* Flat 13-bit offset of the dispatch cell, for addr_capture_wr's own
 * JMP X!=Y branch -- not a wire-protocol constant in its own right (see
 * pc_exp.h's own EXP_INSTRUCTION_PAGE/ADDRESS), so kept local rather than
 * added to the hand-synced pc_exp.h. */
#define EXP_INSTRUCTION_FLAT_ADDR ((EXP_INSTRUCTION_PAGE << 8) | EXP_INSTRUCTION_ADDRESS)

static uint dma_wr_addr_relay, dma_wr_byte_store;
static uint sm_trigger_detect_wr, sm_addr_capture_wr;
static uint sm_data_capture_wr_ordinary, sm_data_capture_wr_dispatch;
static uint off_trig, off_addr, off_data_ord, off_data_disp; /* kept for BusServeRestart() */
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
